giltesa/SmartHome/2. Touch switch/2. Gerbers/1. Touch Switch/Touch Switch - 2017-10 v2.0/Images/SmartHome - Switch Touch.GBO.png

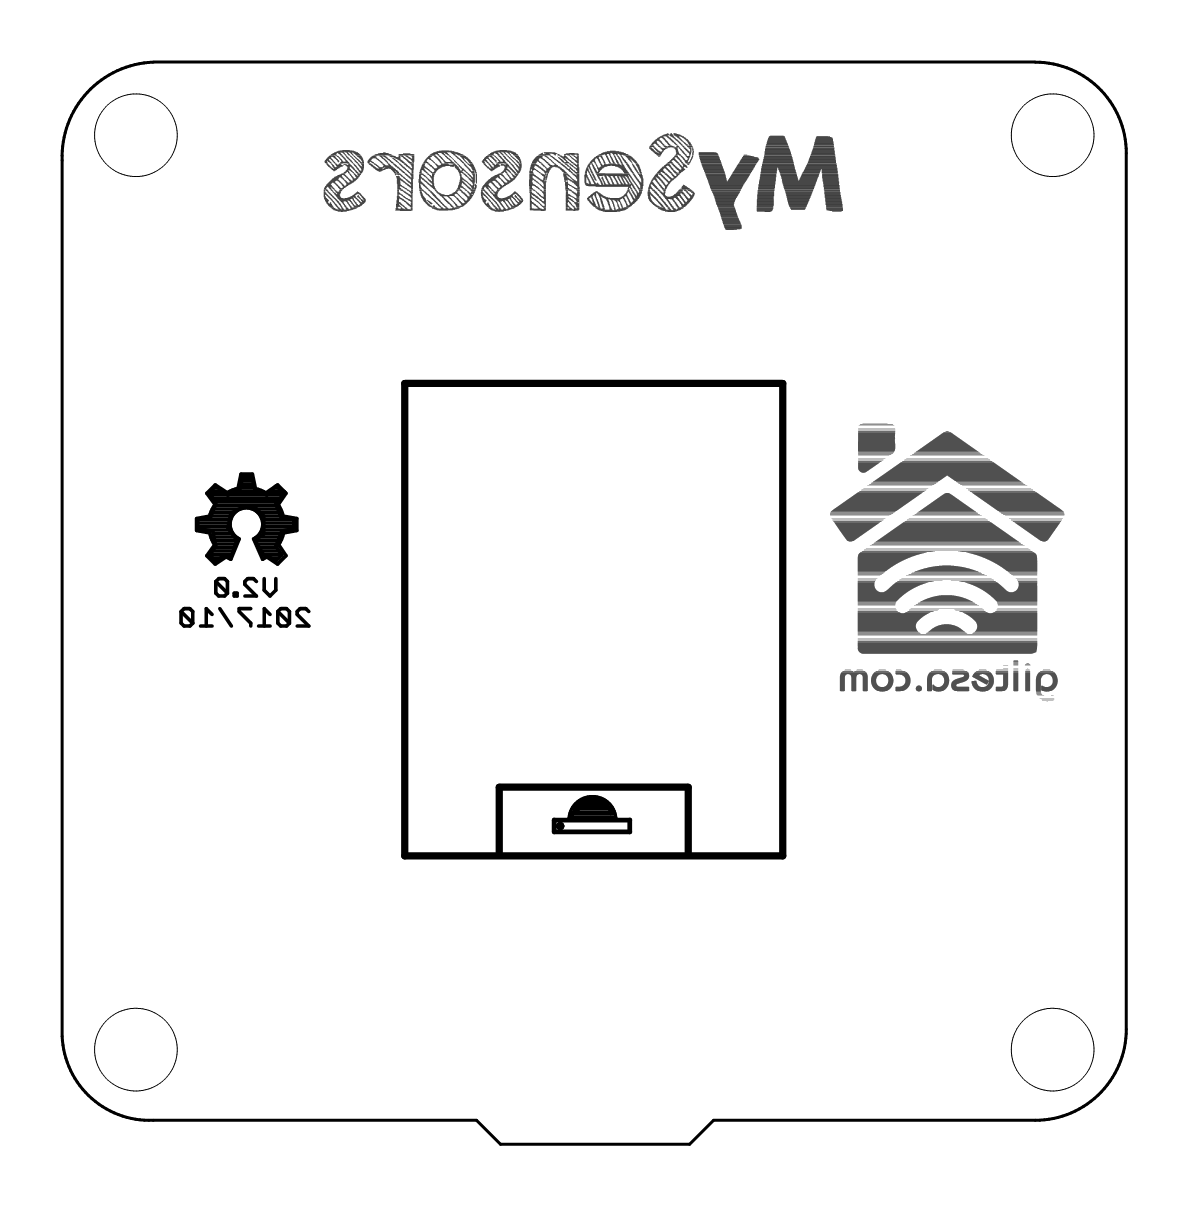
2. Touch switch/2. Gerbers/1. Touch Switch/Touch Switch - 2017-10 v2.0/Images/SmartHome - Switch Touch.GBO.png
