giltesa/SmartHome/2. Touch switch/2. Gerbers/2. Relay Switch/Relay Switch - 2017-10 v1.0/Images/SmartHome - Switch Relay.GBP.png

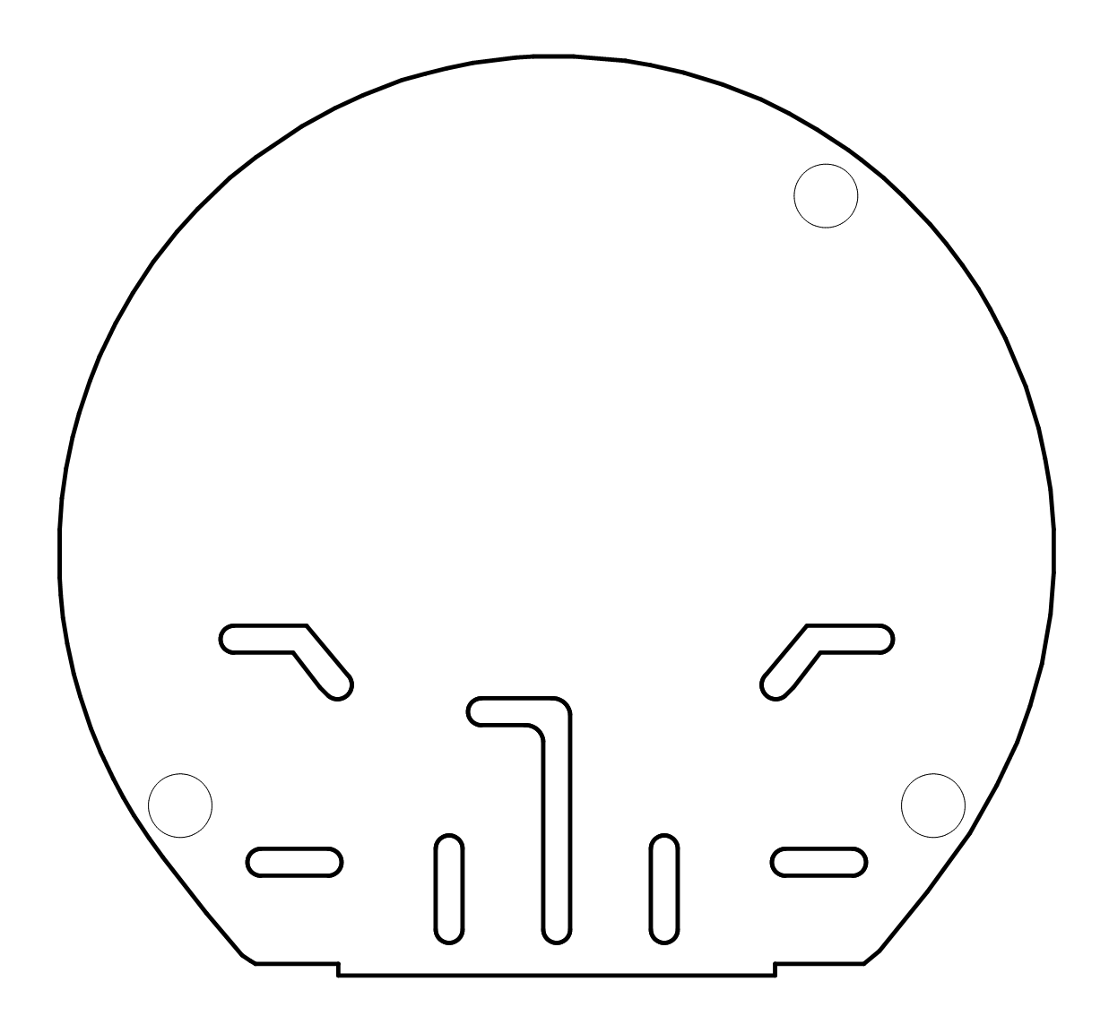
2. Touch switch/2. Gerbers/2. Relay Switch/Relay Switch - 2017-10 v1.0/Images/SmartHome - Switch Relay.GBP.png
