giltesa/SmartHome/2. Touch switch/2. Gerbers/2. Relay Switch/Relay Switch - 2017-12 v1.1/Images/SmartHome - Switch Relay.GTO.png

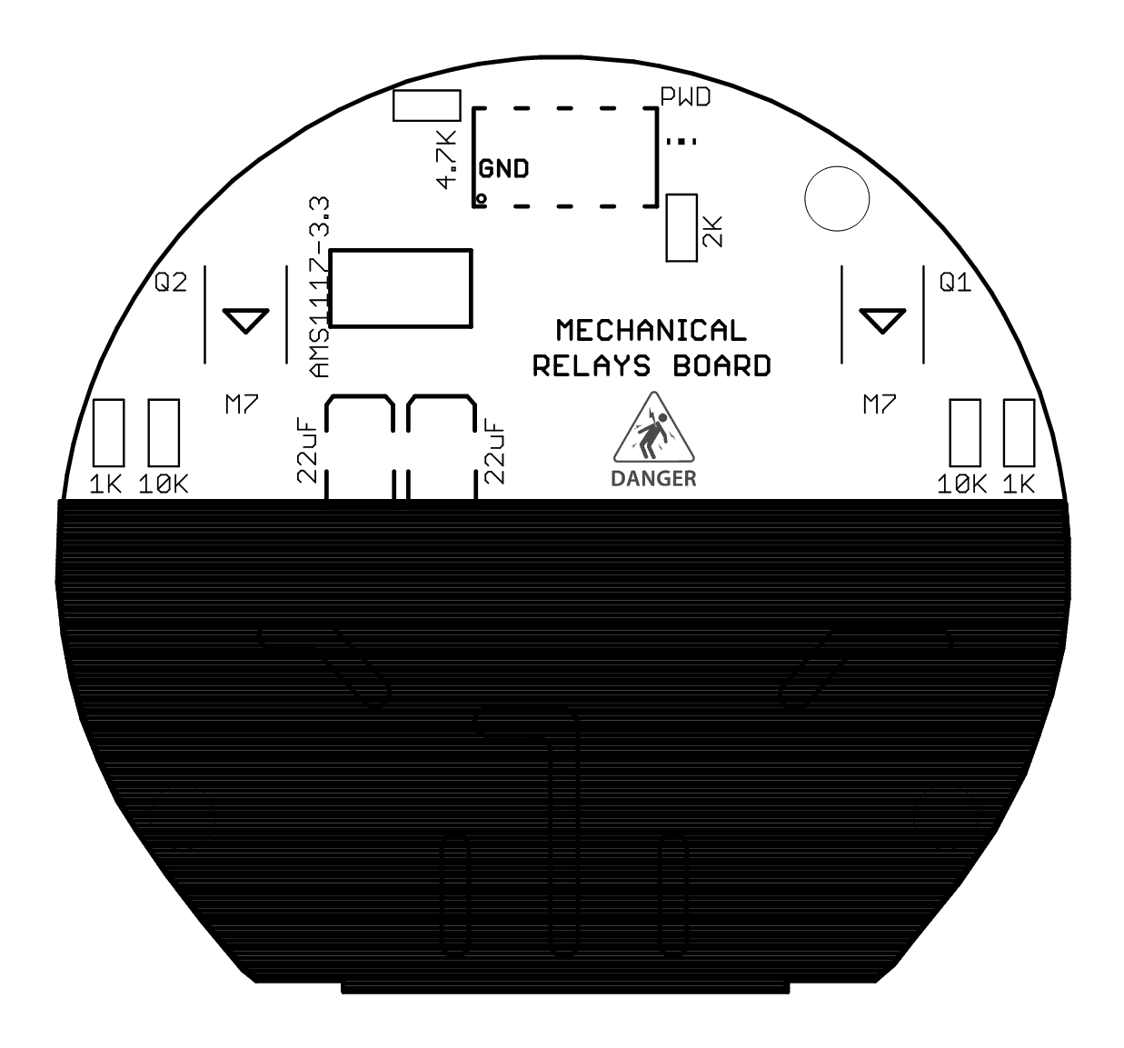
2. Touch switch/2. Gerbers/2. Relay Switch/Relay Switch - 2017-12 v1.1/Images/SmartHome - Switch Relay.GTO.png
