giltesa/SmartHome/2. Touch switch/2. Gerbers/2. Relay Switch/Relay Switch - 2018-03 v1.2/Images/Relay Switch.GBP.png

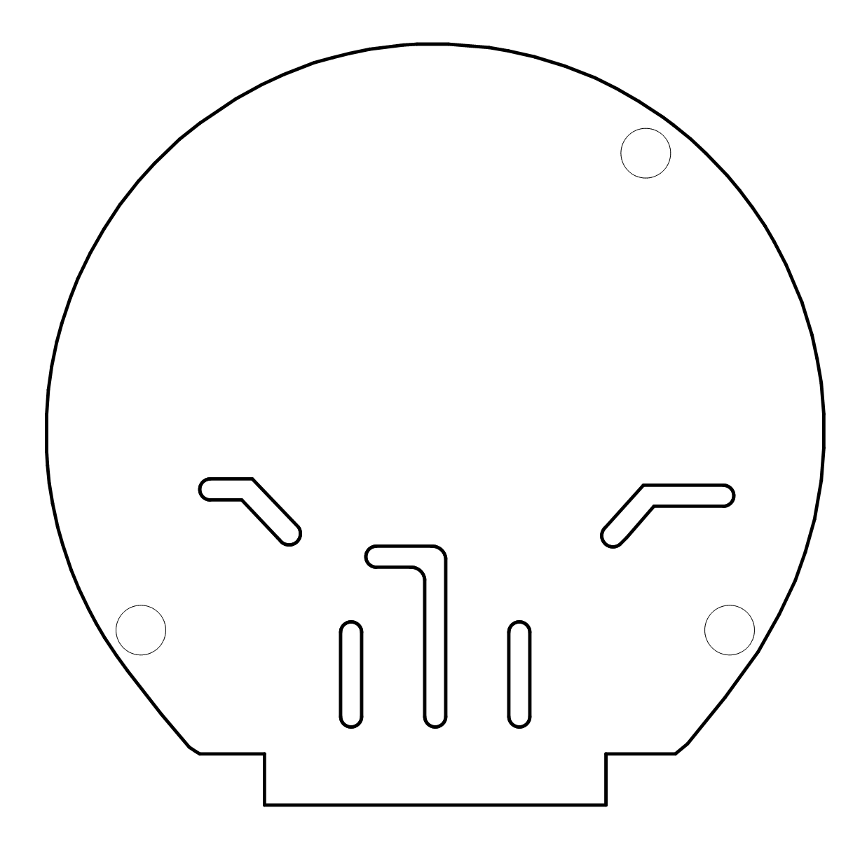
2. Touch switch/2. Gerbers/2. Relay Switch/Relay Switch - 2018-03 v1.2/Images/Relay Switch.GBP.png
