giltesa/SmartHome/2. Touch switch/2. Gerbers/3. Triac Switch/Triac Switch - 2018-03 v1.0/Images/SmartHome - Triac Switch.GTL.png

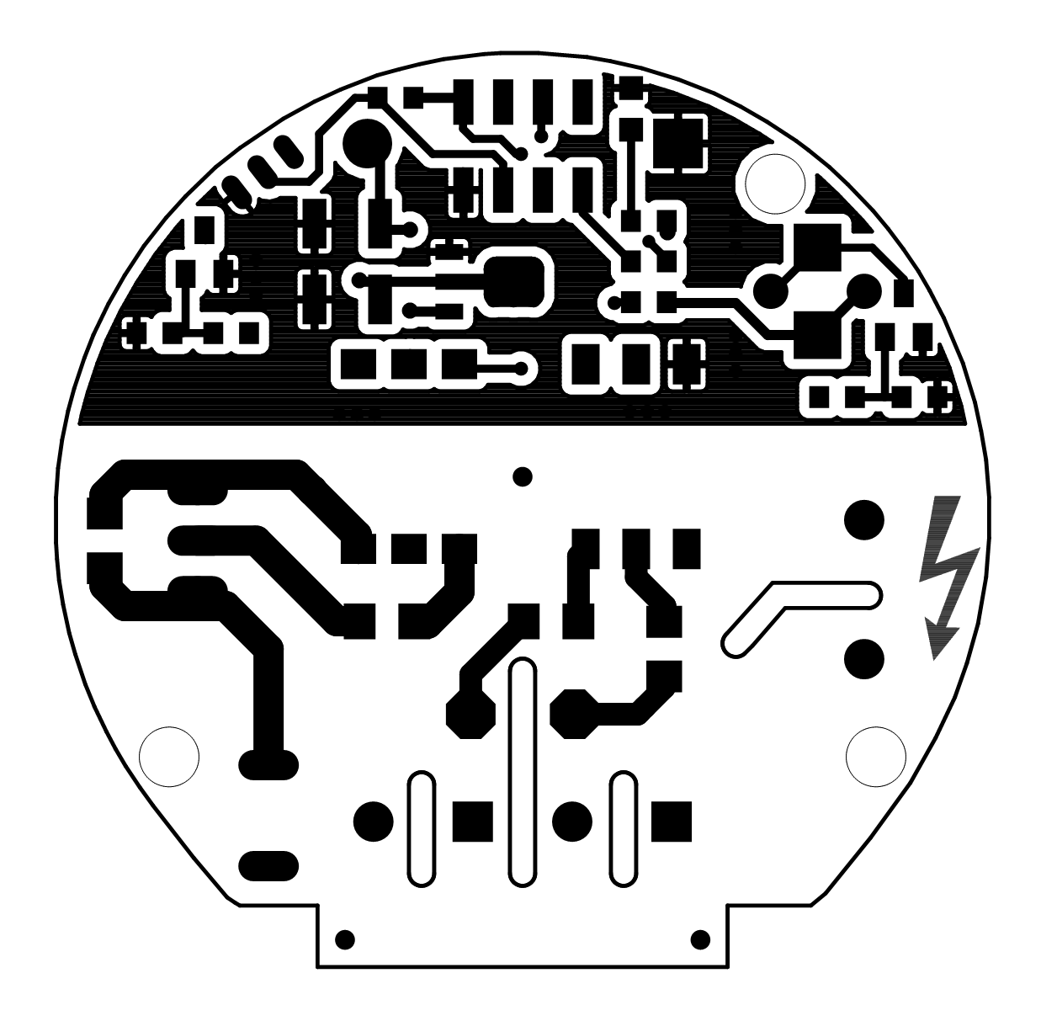
2. Touch switch/2. Gerbers/3. Triac Switch/Triac Switch - 2018-03 v1.0/Images/SmartHome - Triac Switch.GTL.png
