giltesa/SmartHome/2. Touch switch/3. Renders/2. Relay Switch_1.png

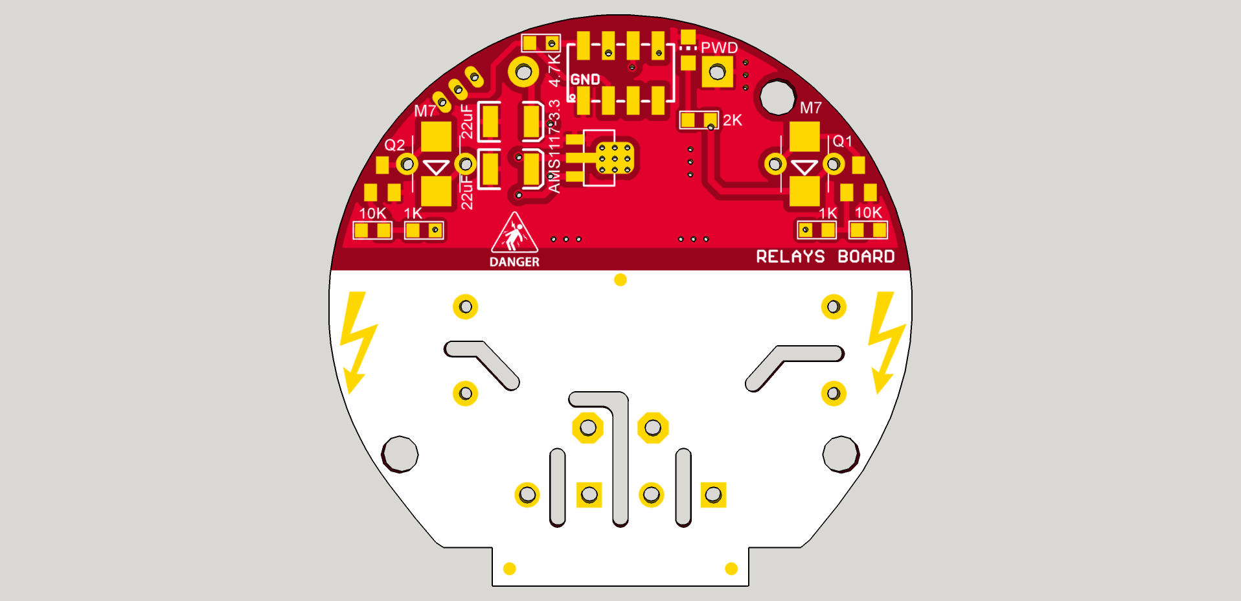
2. Touch switch/3. Renders/2. Relay Switch_1.png
