giltesa/SmartHome/2. Touch switch/3. Renders/2. Relay Switch_2.png

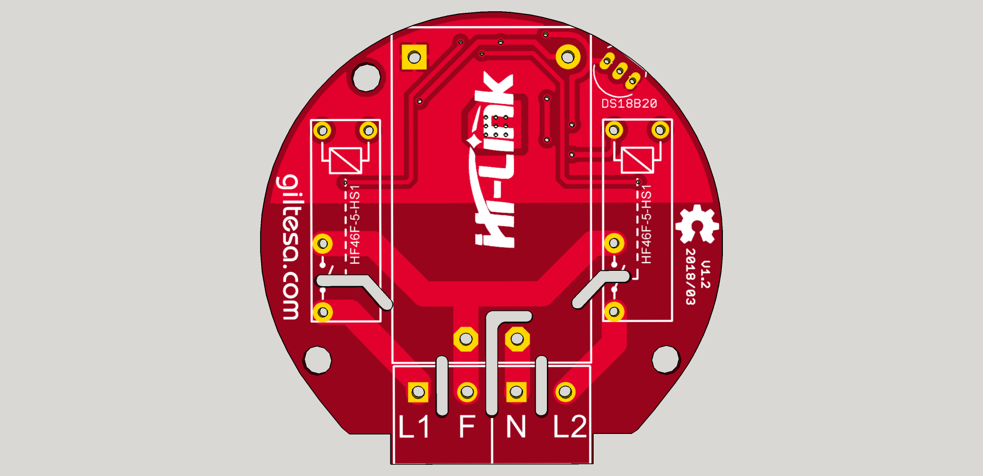
2. Touch switch/3. Renders/2. Relay Switch_2.png
