giltesa/SmartHome/2. Touch switch/3. Renders/Sketchup Enclosure/Switch Relay v3.png

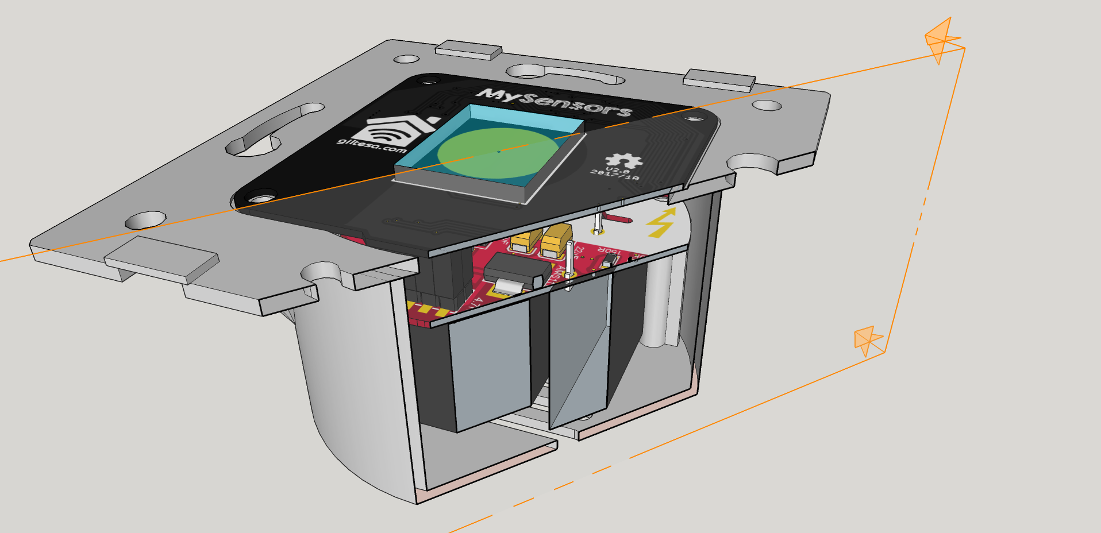
2. Touch switch/3. Renders/Sketchup Enclosure/Switch Relay v3.png
