giltesa/SmartHome/2. Touch switch/3. Renders/Touch Switch.png

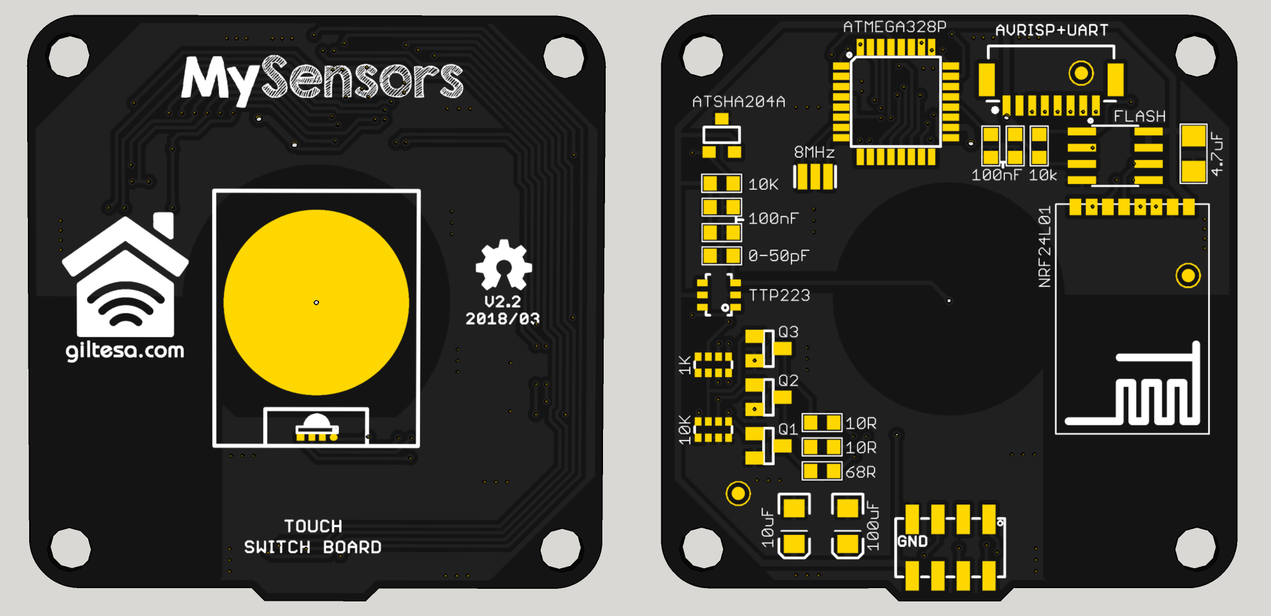
2. Touch switch/3. Renders/Touch Switch.png
