giltesa/SmartHome/2. Touch switch/4. Documentation/1. MCU Board/Fuses ATmega328p 8Mhz 3.3V_1.png

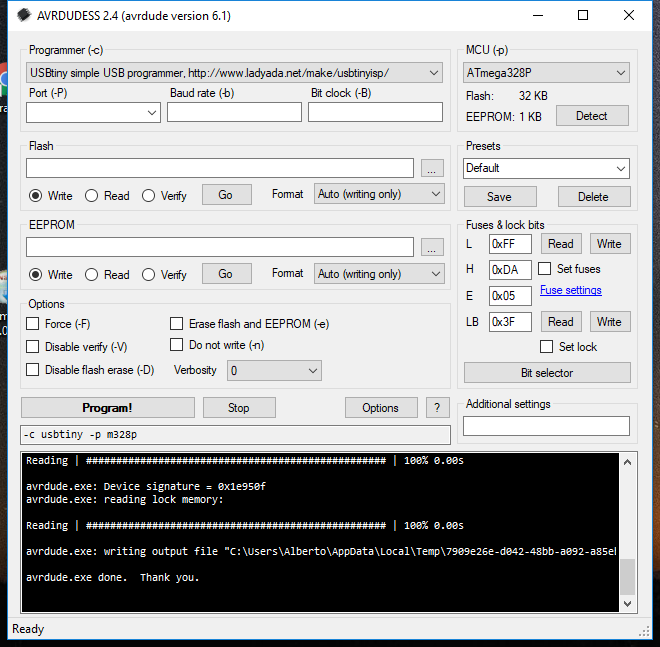
2. Touch switch/4. Documentation/1. MCU Board/Fuses ATmega328p 8Mhz 3.3V_1.png
