giltesa/SmartHome/2. Touch switch/4. Documentation/1. MCU Board/LED RGB.JPG

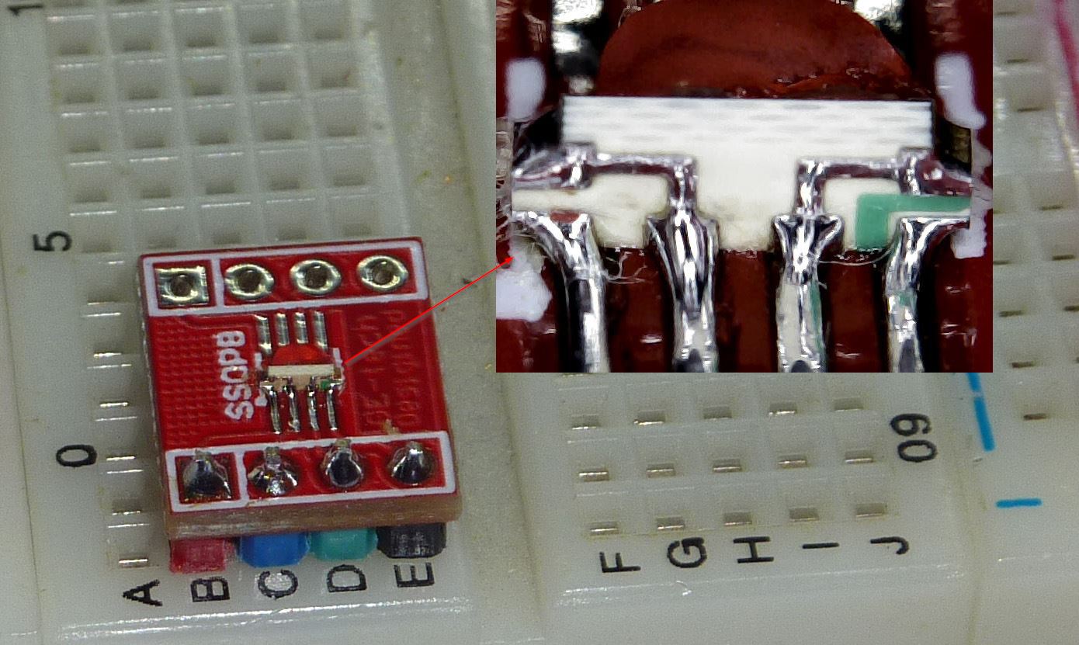
2. Touch switch/4. Documentation/1. MCU Board/LED RGB.JPG
