giltesa/SmartHome/2. Touch switch/4. Documentation/2. Relay Board/Connector AC 5mm.jpg

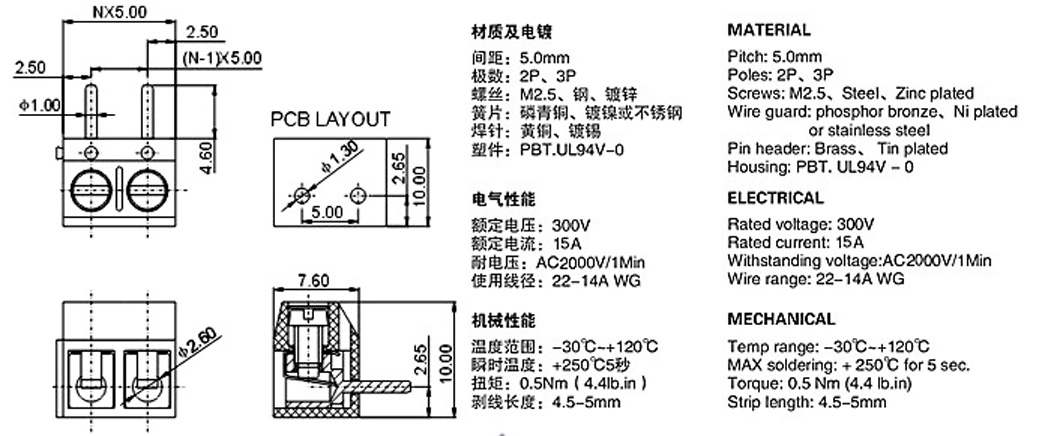
2. Touch switch/4. Documentation/2. Relay Board/Connector AC 5mm.jpg
