giltesa/SmartHome/2. Touch switch/6. Photos/Smarthome_Touch_Switch_Relay_05.JPG

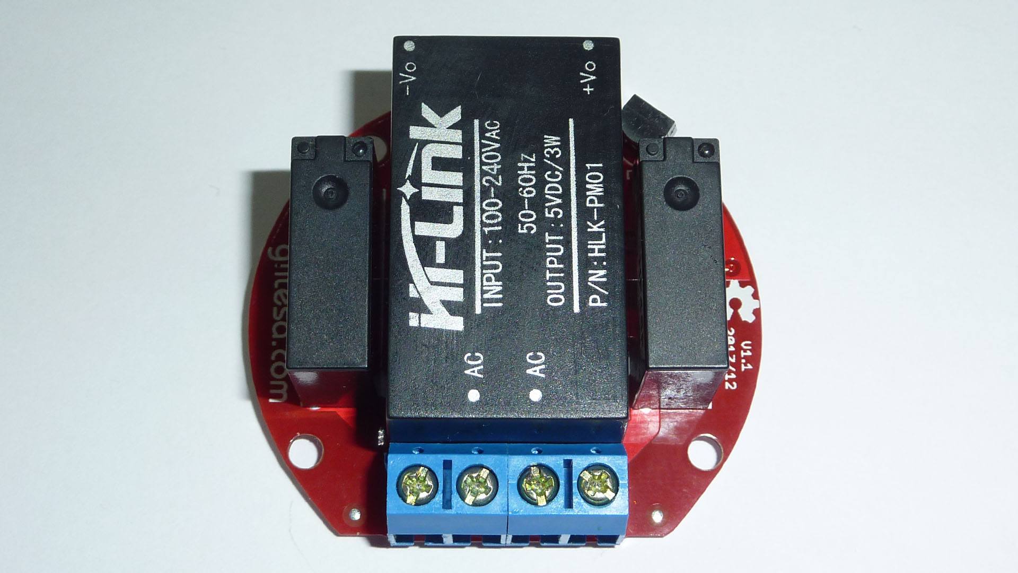
2. Touch switch/6. Photos/Smarthome_Touch_Switch_Relay_05.JPG
