giltesa/SmartHome/3. Sensor/2. Gerbers/Images/Sensor.GBL.png

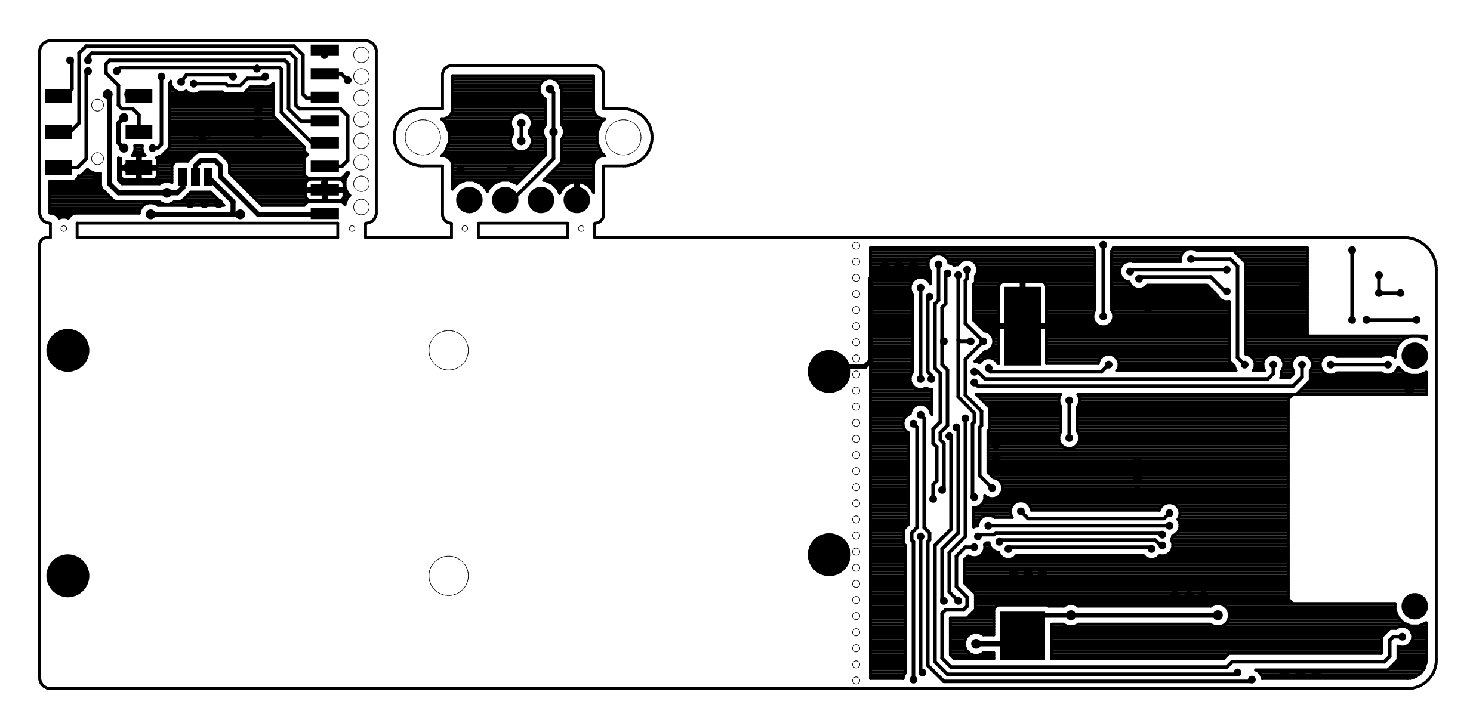
3. Sensor/2. Gerbers/Images/Sensor.GBL.png
