giltesa/SmartHome/3. Sensor/2. Gerbers/Images/Sensor.GBO.png

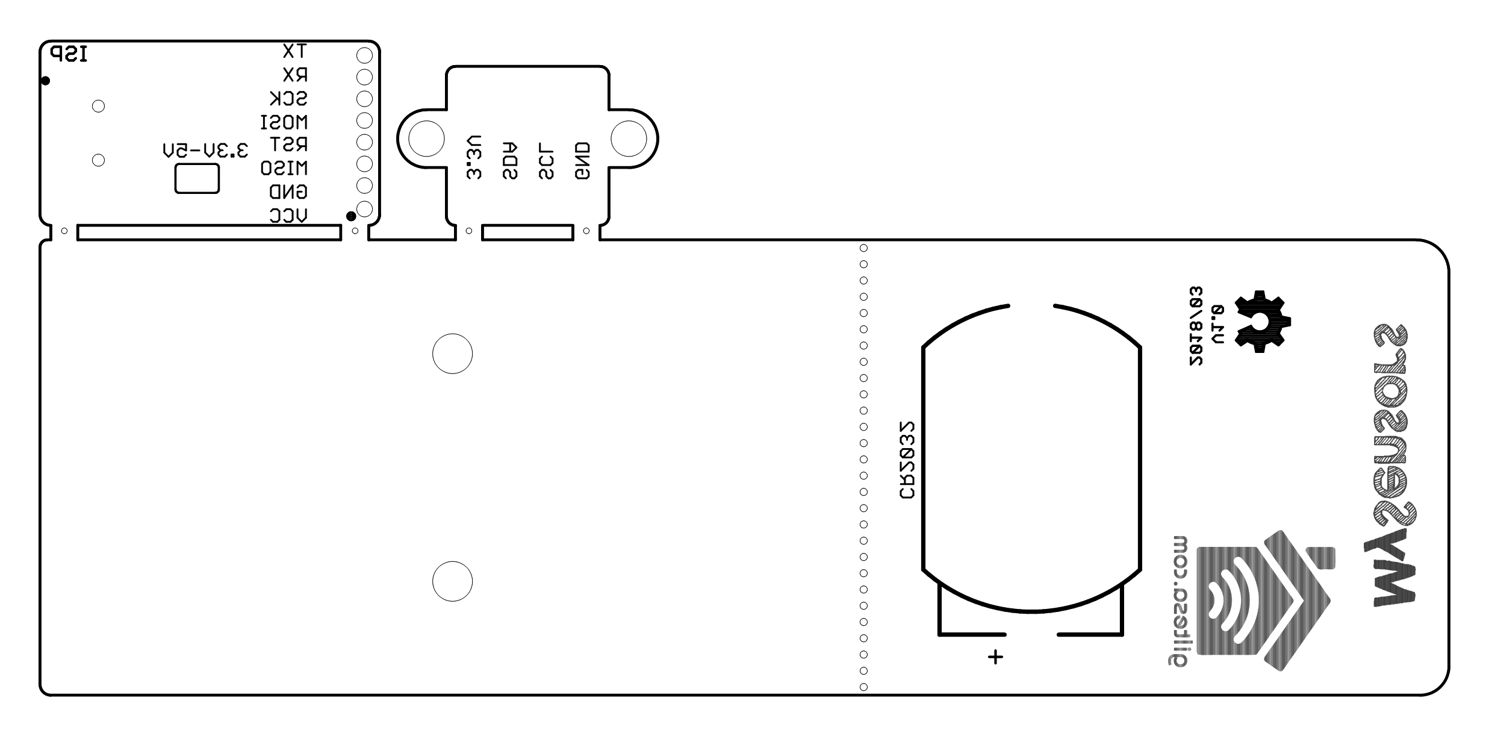
3. Sensor/2. Gerbers/Images/Sensor.GBO.png
