giltesa/SmartHome/3. Sensor/2. Gerbers/Images/Sensor.GBP.png

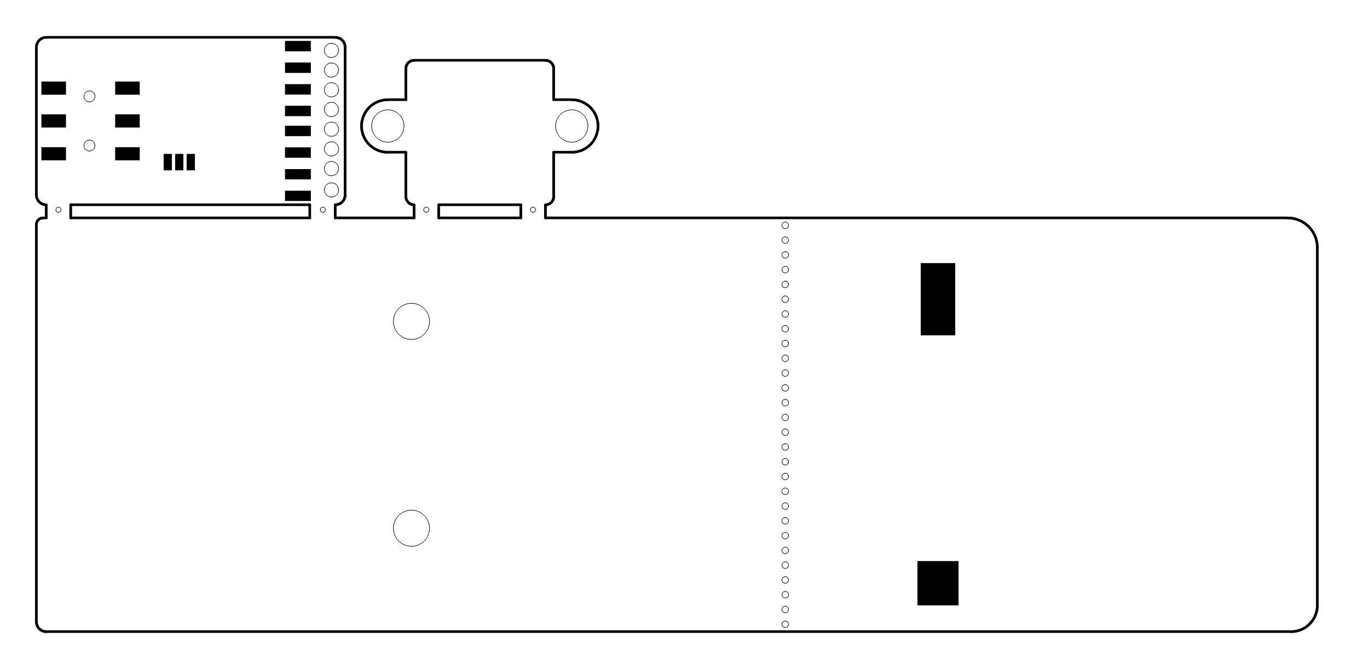
3. Sensor/2. Gerbers/Images/Sensor.GBP.png
