giltesa/SmartHome/3. Sensor/2. Gerbers/Images/Sensor.GBS.png

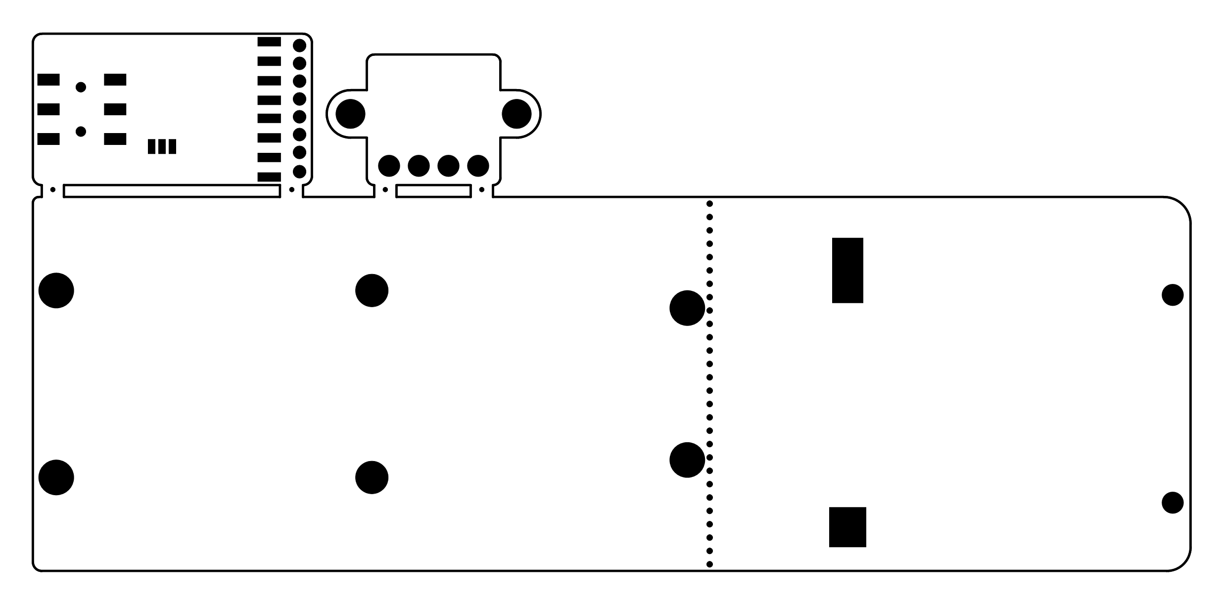
3. Sensor/2. Gerbers/Images/Sensor.GBS.png
