giltesa/SmartHome/3. Sensor/2. Gerbers/Images/Sensor.GML.png

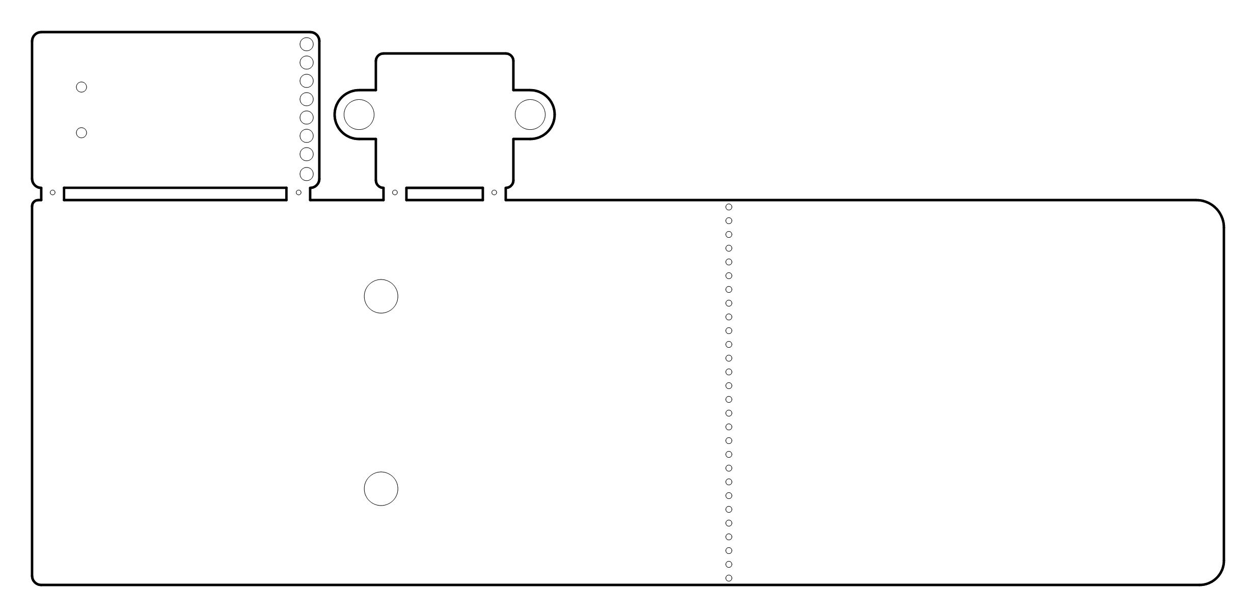
3. Sensor/2. Gerbers/Images/Sensor.GML.png
