giltesa/SmartHome/3. Sensor/2. Gerbers/Images/Sensor.GTL.png

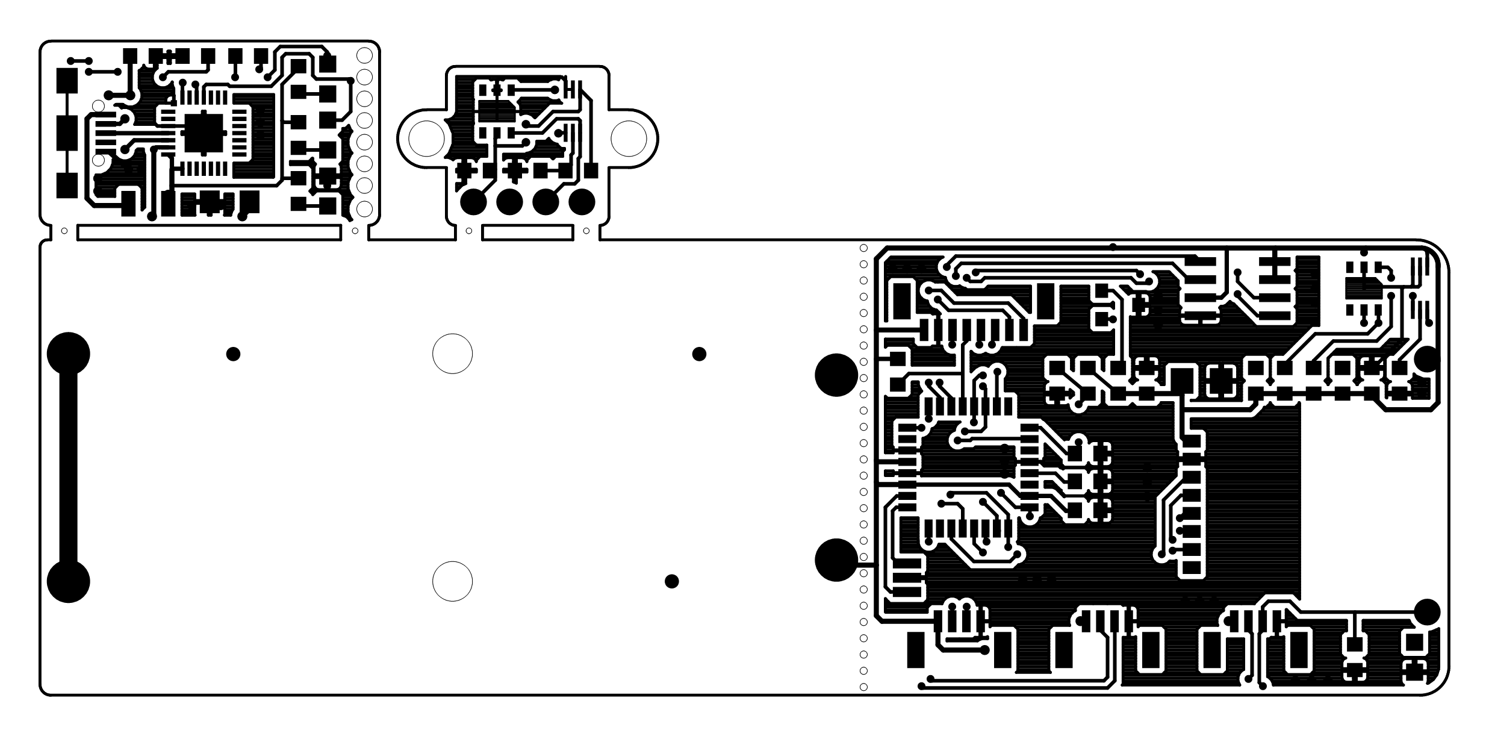
3. Sensor/2. Gerbers/Images/Sensor.GTL.png
