giltesa/SmartHome/3. Sensor/2. Gerbers/Images/Sensor.GTP.png

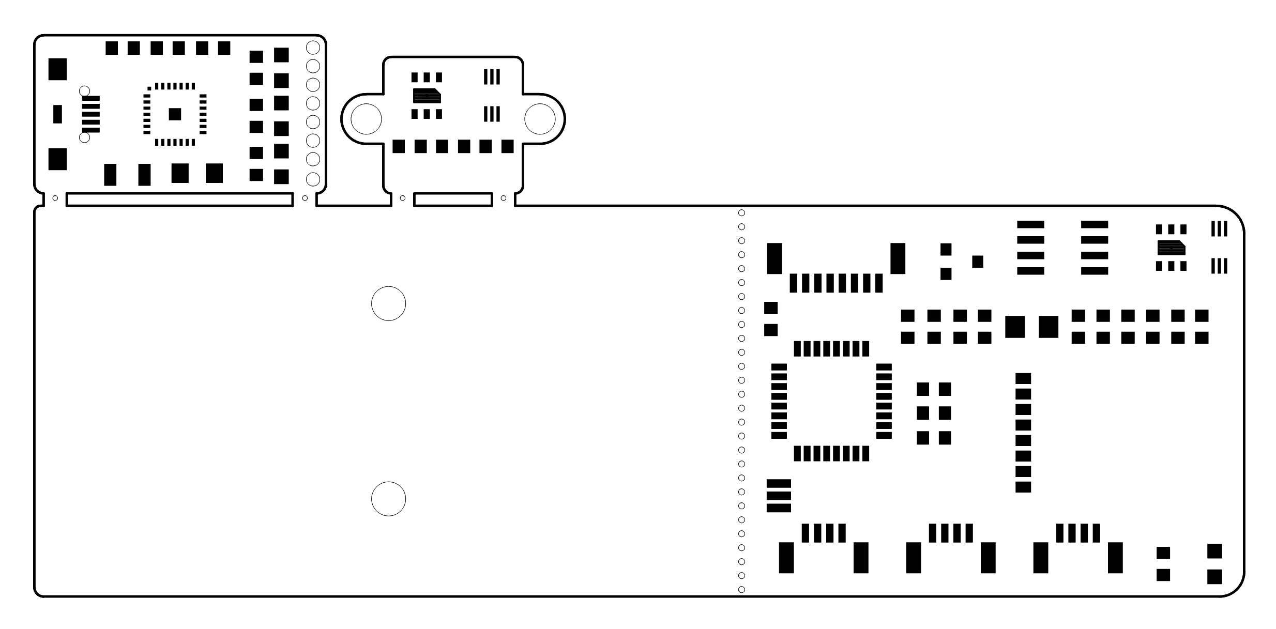
3. Sensor/2. Gerbers/Images/Sensor.GTP.png
