giltesa/SmartHome/3. Sensor/2. Gerbers/Images/Sensor.GTS.png

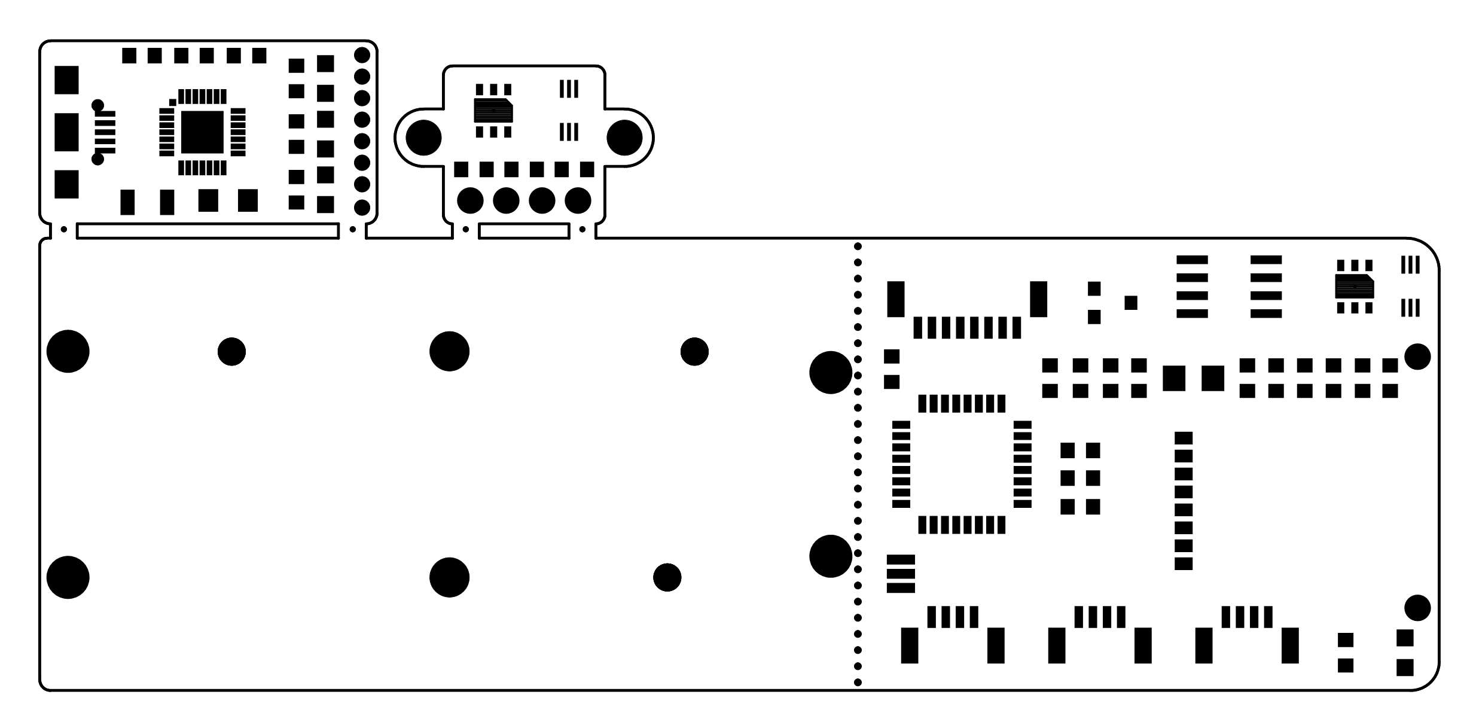
3. Sensor/2. Gerbers/Images/Sensor.GTS.png
