giltesa/SmartHome/3. Sensor/3. Renders/Sensor_1.png

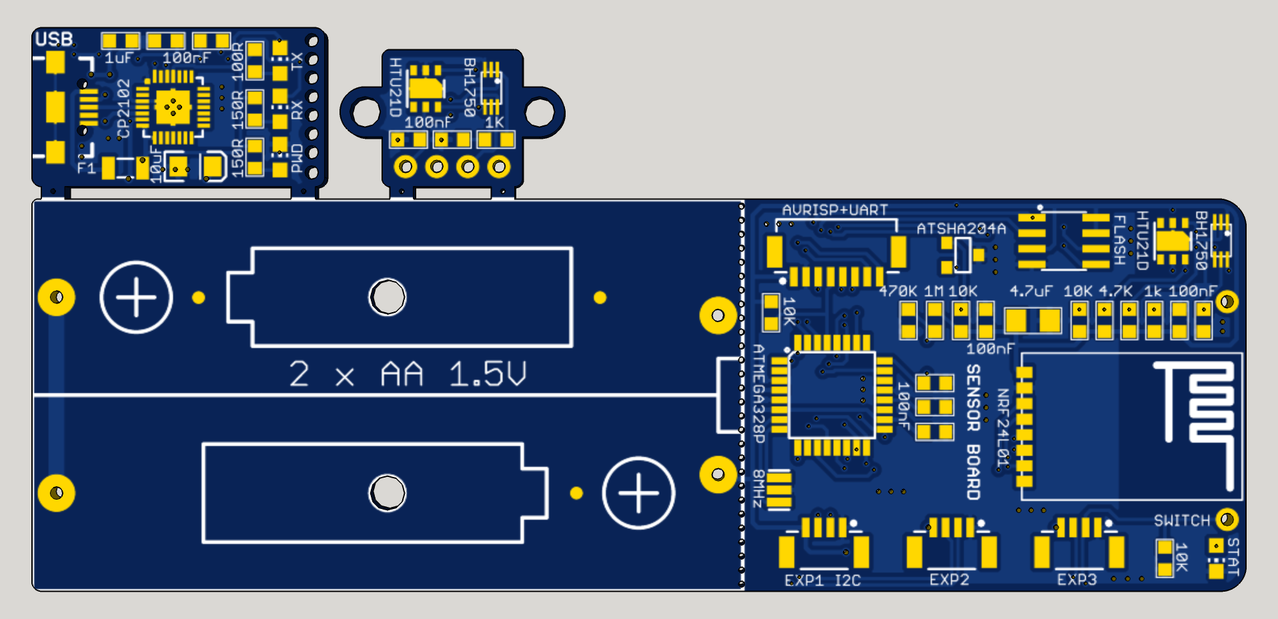
3. Sensor/3. Renders/Sensor_1.png
