giltesa/SmartHome/3. Sensor/3. Renders/Sensor_2.png

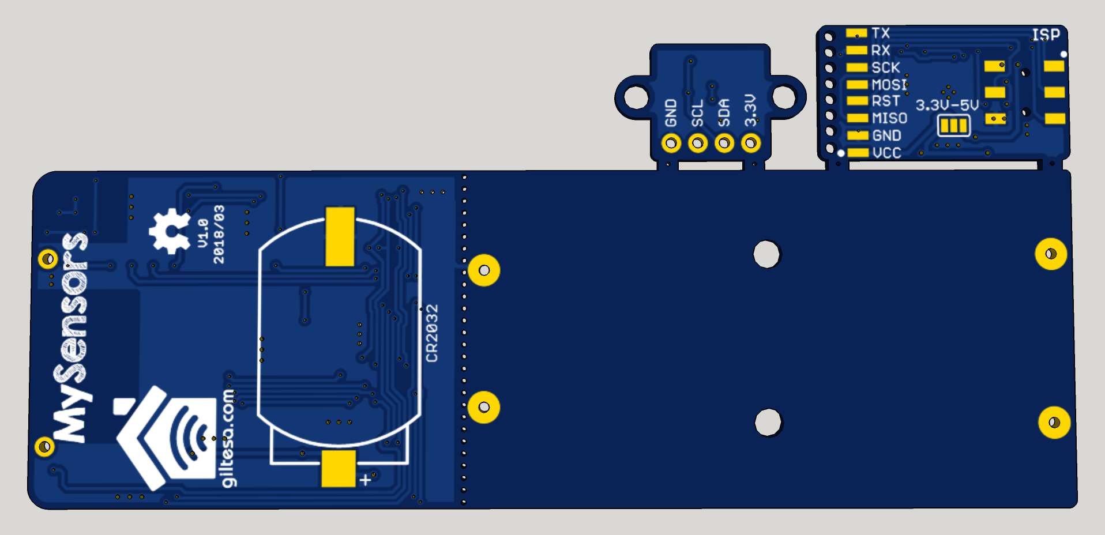
3. Sensor/3. Renders/Sensor_2.png
