giltesa/SmartHome/3. Sensor/6. Photos/External programmer 1.jpg

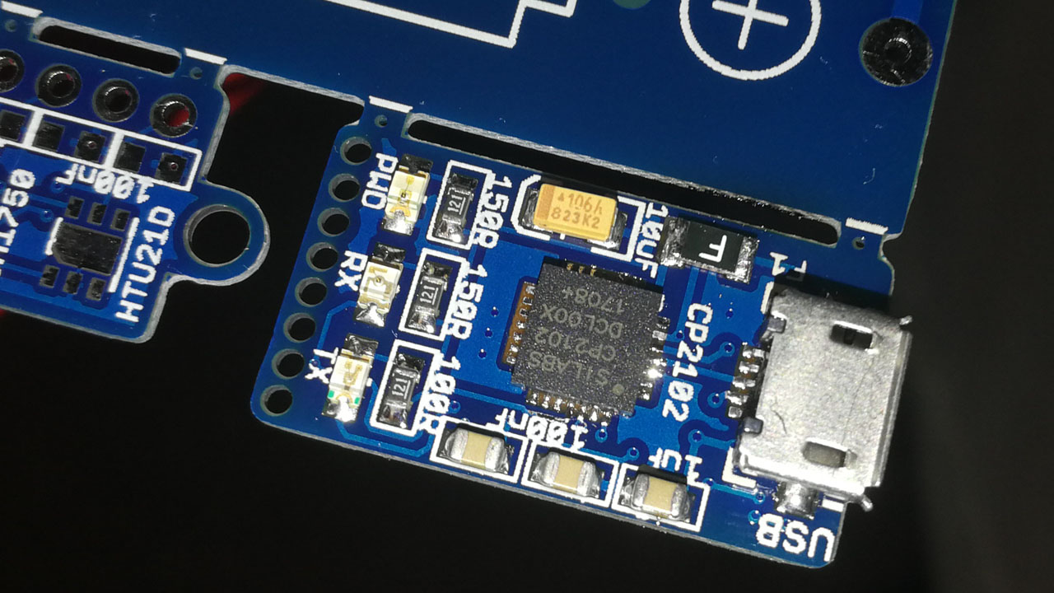
3. Sensor/6. Photos/External programmer 1.jpg
