giltesa/SmartHome/3. Sensor/6. Photos/External programmer 2 ISP.jpg

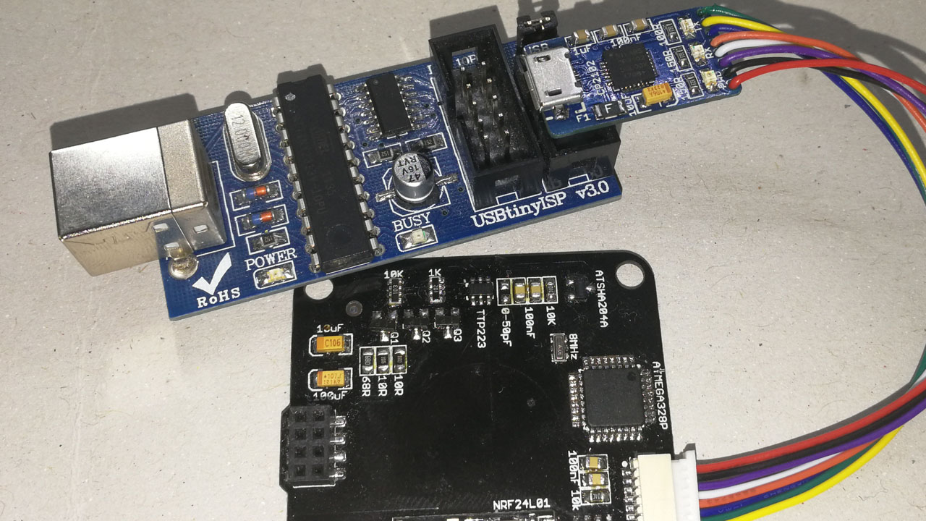
3. Sensor/6. Photos/External programmer 2 ISP.jpg
