giltesa/SmartHome/3. Sensor/6. Photos/External programmer 3 UART.jpg

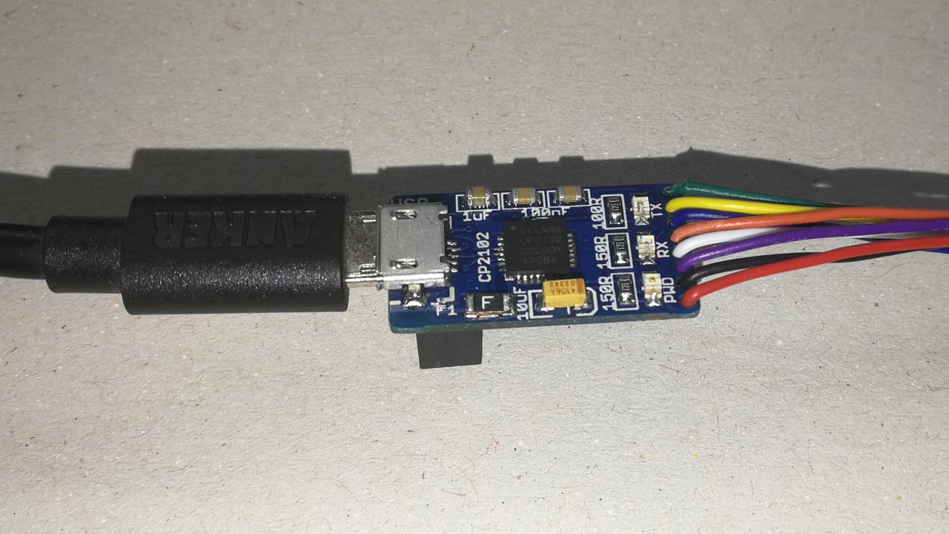
3. Sensor/6. Photos/External programmer 3 UART.jpg
