giltesa/SmartHome/3. Sensor/6. Photos/Sensor 1.jpg

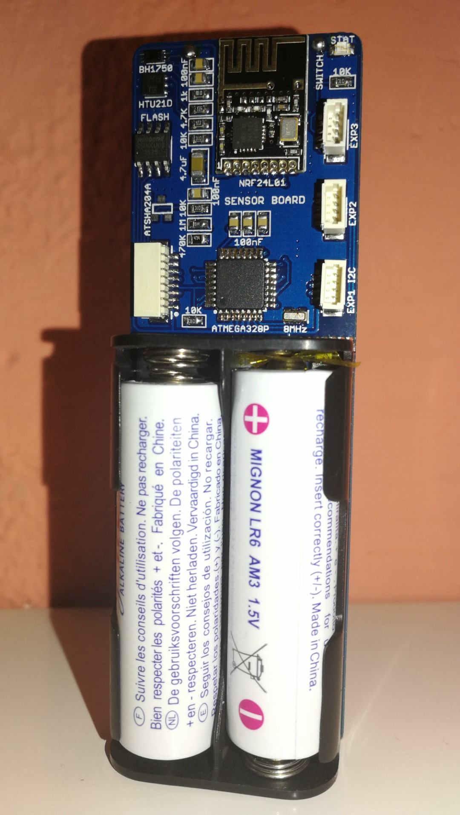
3. Sensor/6. Photos/Sensor 1.jpg
