giltesa/SmartHome/3. Sensor/6. Photos/Sensor 2.jpg

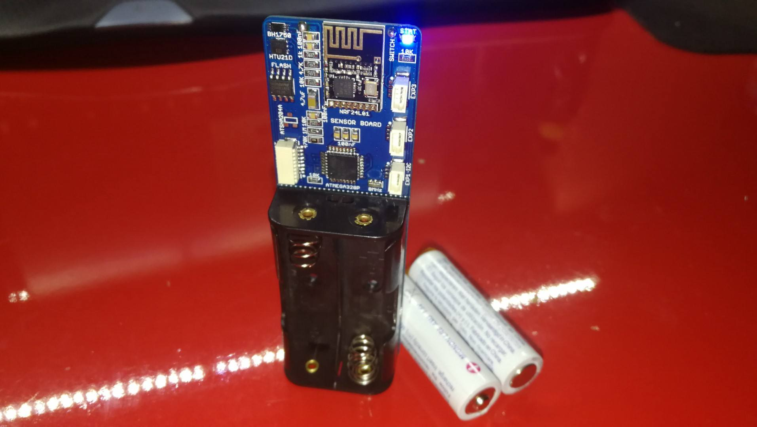
3. Sensor/6. Photos/Sensor 2.jpg
