giltesa/SmartHome/3. Sensor/6. Photos/Sensor 3.jpg

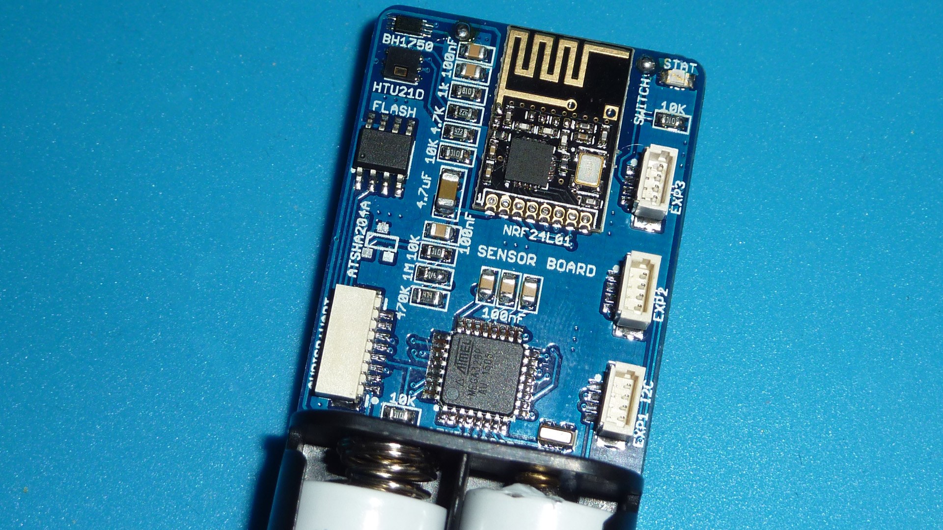
3. Sensor/6. Photos/Sensor 3.jpg
