giltesa/SmartHome/4. Remote Control/2. Gerbers/Images/Remote Control - x2.GBP.png

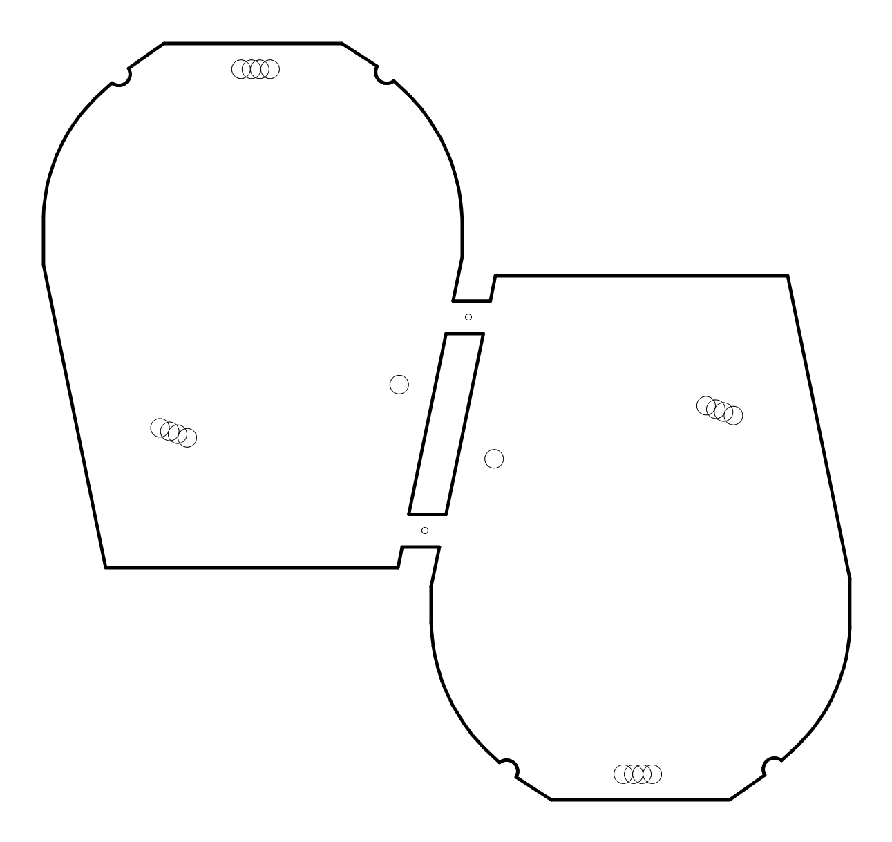
4. Remote Control/2. Gerbers/Images/Remote Control - x2.GBP.png
