giltesa/SmartHome/4. Remote Control/2. Gerbers/Images/Remote Control - x2.GTO.png

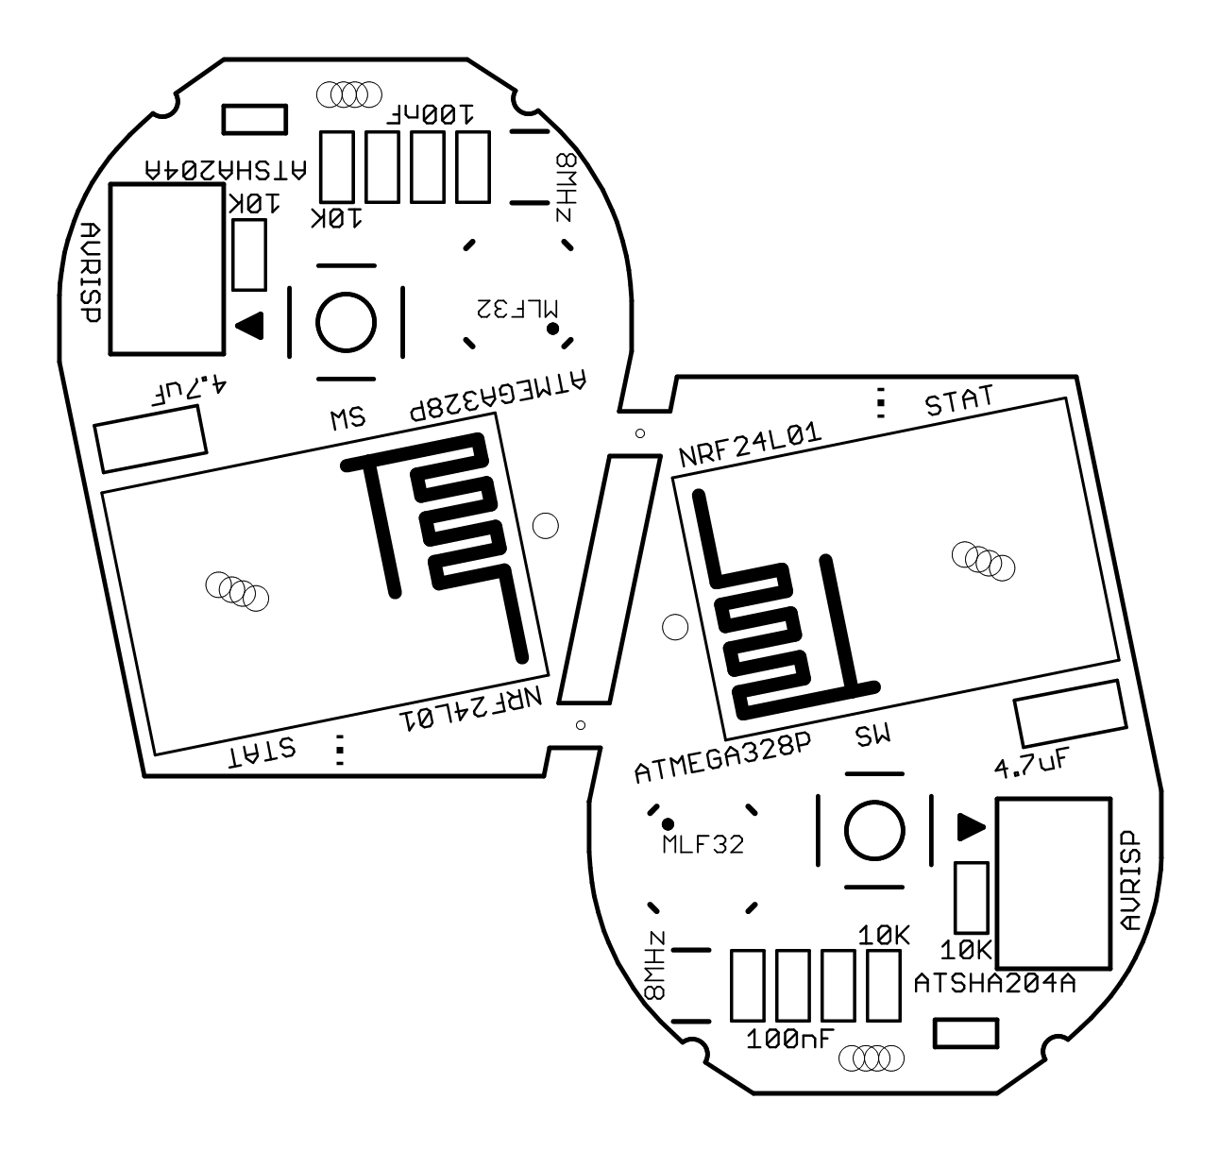
4. Remote Control/2. Gerbers/Images/Remote Control - x2.GTO.png
