giltesa/SmartHome/4. Remote Control/2. Gerbers/Images/Remote Control - x2.GTP.png

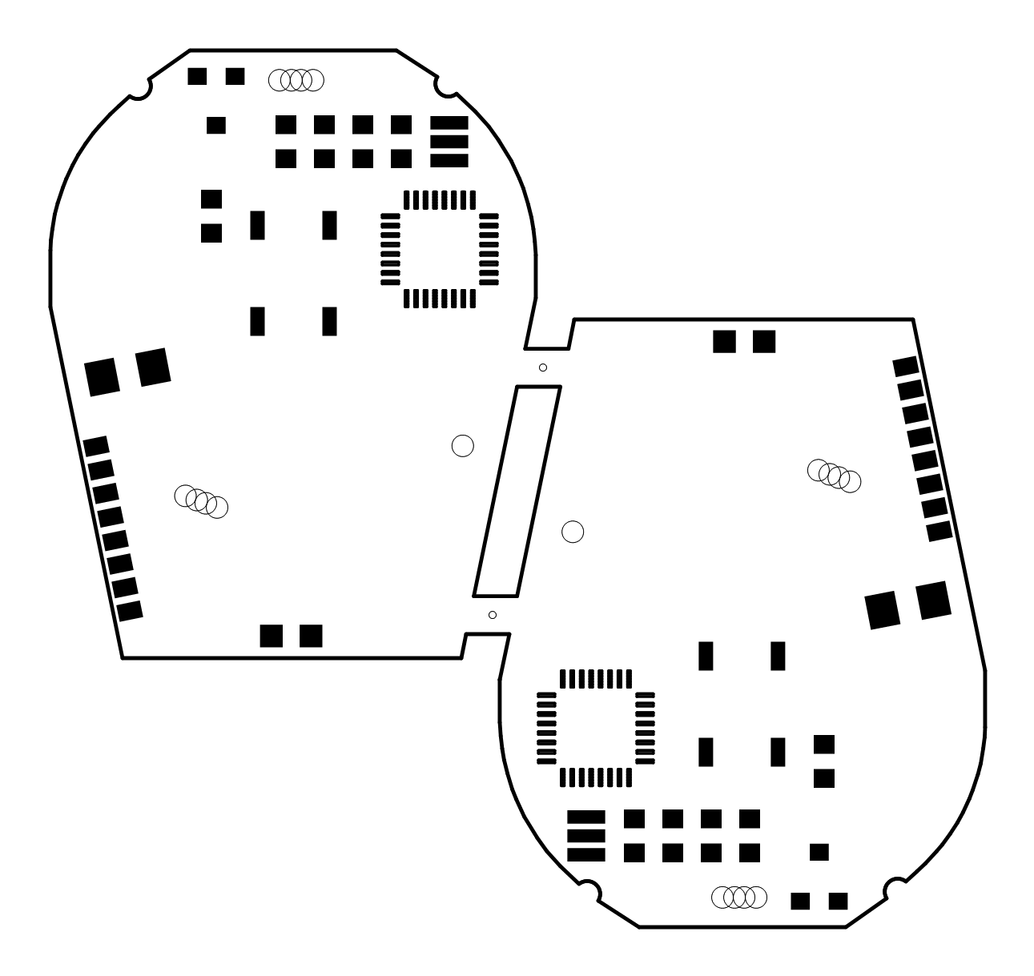
4. Remote Control/2. Gerbers/Images/Remote Control - x2.GTP.png
