giltesa/SmartHome/4. Remote Control/2. Gerbers/Images/Remote Control - x2.GTS.png

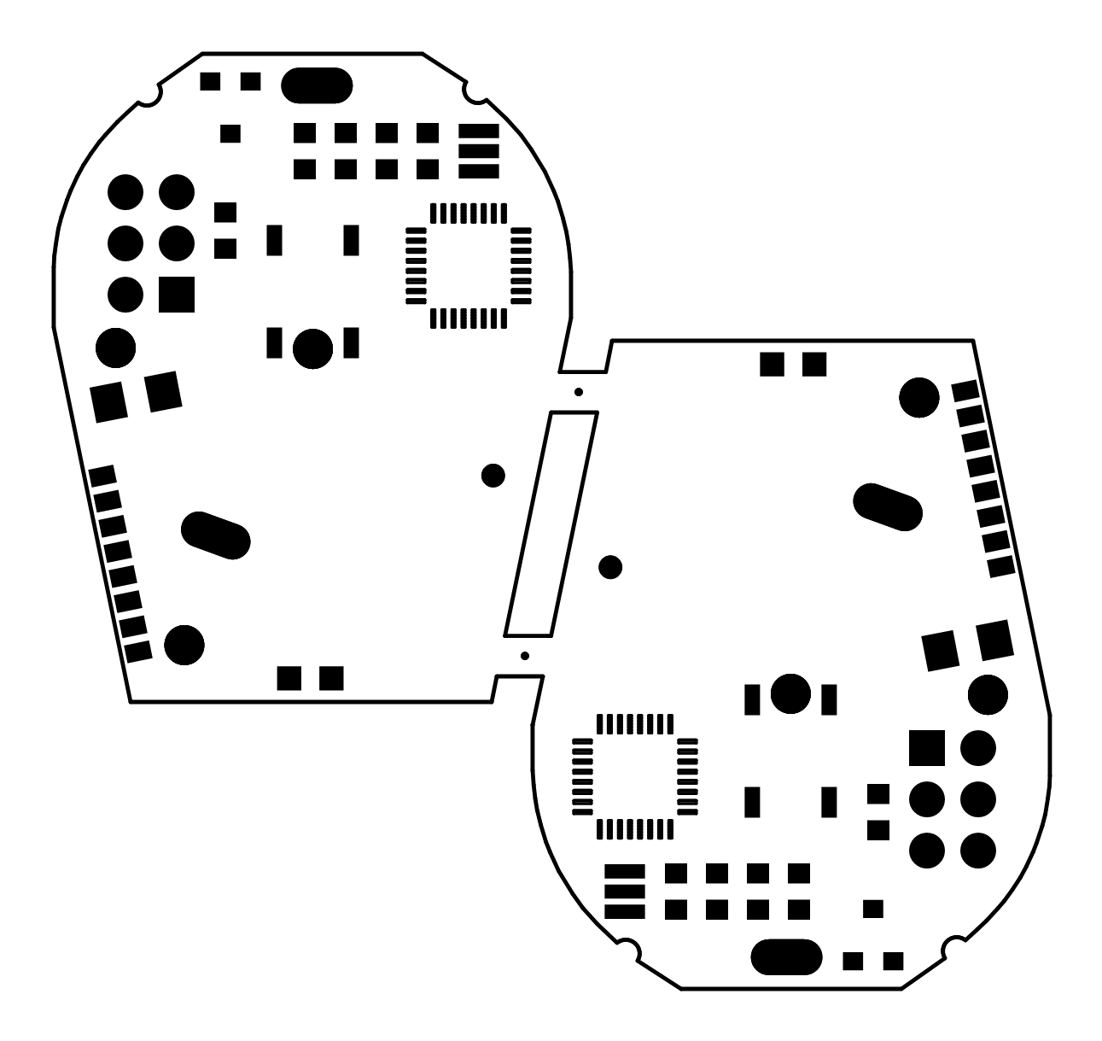
4. Remote Control/2. Gerbers/Images/Remote Control - x2.GTS.png
