giltesa/SmartHome/4. Remote Control/3. Renders/Remote Control RF 1.png

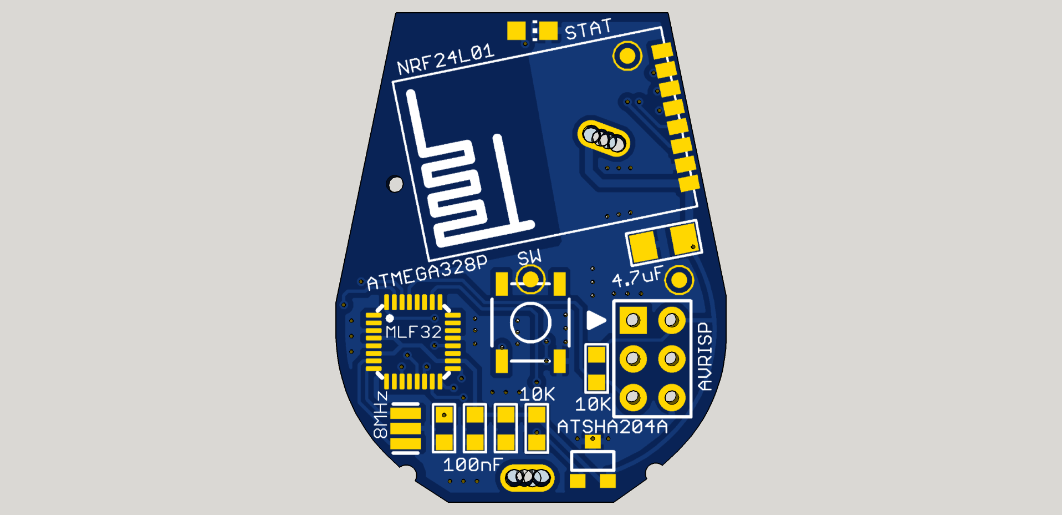
4. Remote Control/3. Renders/Remote Control RF 1.png
