giltesa/SmartHome/4. Remote Control/3. Renders/Remote Control RF 2.png

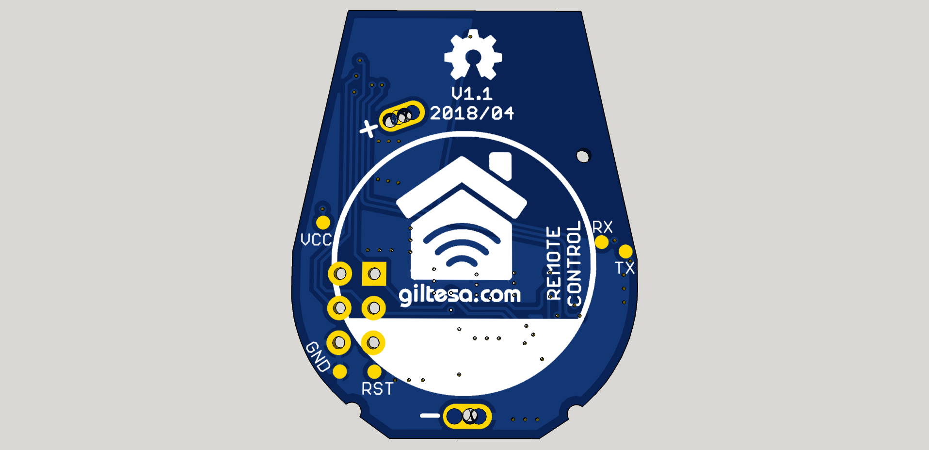
4. Remote Control/3. Renders/Remote Control RF 2.png
