giltesa/SmartHome/4. Remote Control/3. Renders/Remote Control RF 3.png

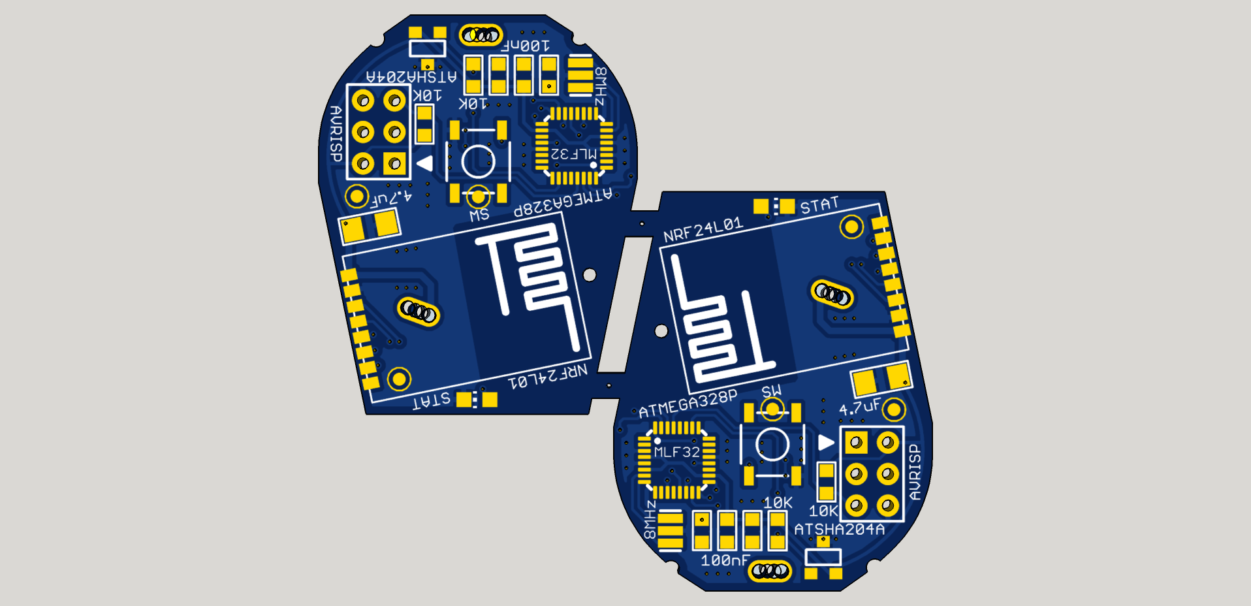
4. Remote Control/3. Renders/Remote Control RF 3.png
