giltesa/SmartHome/4. Remote Control/6. Photos/Catch3602.jpg

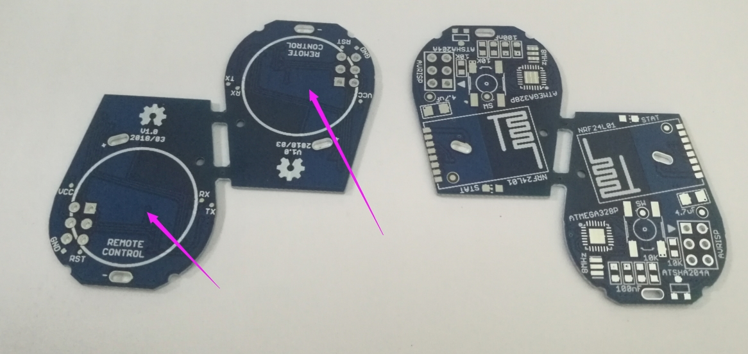
4. Remote Control/6. Photos/Catch3602.jpg
