giltesa/SmartHome/5. LED RGBW Controller/2. Gerbers/Images/LED RGBW Controller.GBL.png

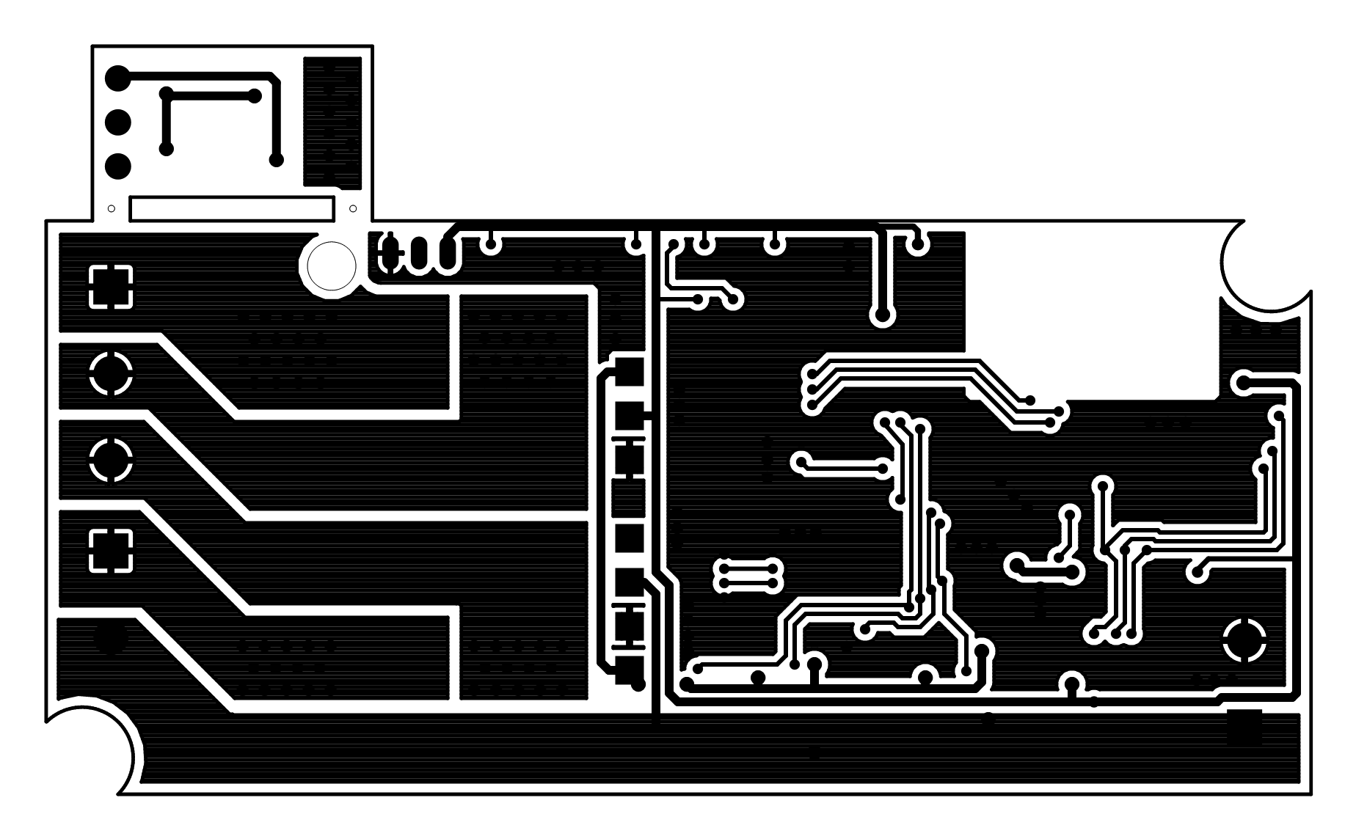
5. LED RGBW Controller/2. Gerbers/Images/LED RGBW Controller.GBL.png
