giltesa/SmartHome/5. LED RGBW Controller/2. Gerbers/Images/LED RGBW Controller.GBP.png

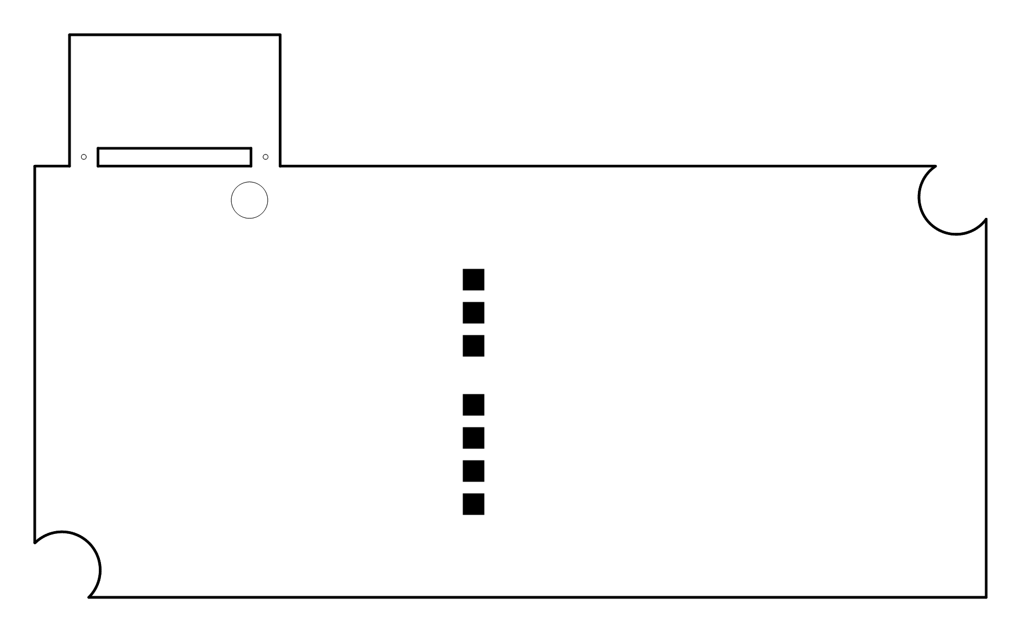
5. LED RGBW Controller/2. Gerbers/Images/LED RGBW Controller.GBP.png
