giltesa/SmartHome/5. LED RGBW Controller/3. Renders/RGBW Controller_2b.png

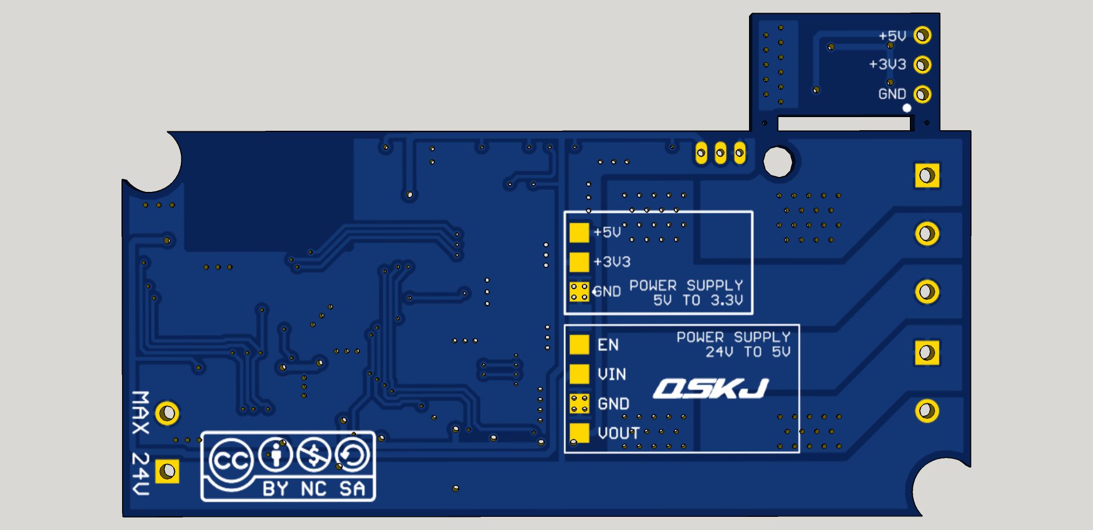
5. LED RGBW Controller/3. Renders/RGBW Controller_2b.png
