giltesa/SmartHome/5. LED RGBW Controller/3. Renders/Sketchup/washer.jpg

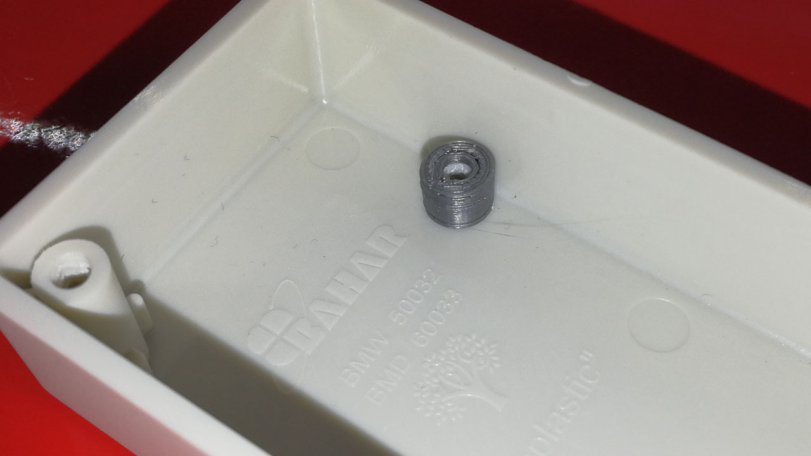
5. LED RGBW Controller/3. Renders/Sketchup/washer.jpg
