giltesa/SmartHome/5. LED RGBW Controller/6. Photos/LED RGBW Controller 4.JPG

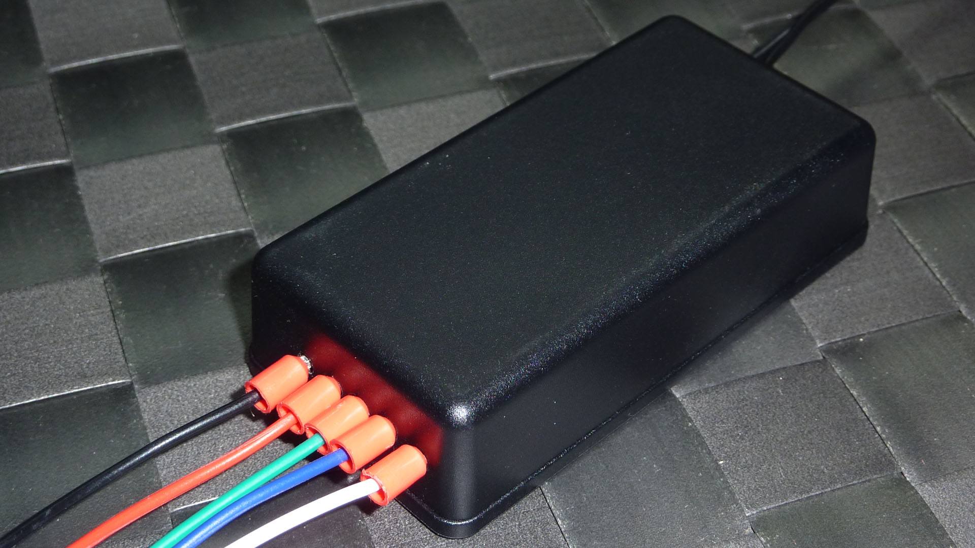
5. LED RGBW Controller/6. Photos/LED RGBW Controller 4.JPG
