giltesa/SmartHome/5. LED RGBW Controller/6. Photos/LED RGBW Controller 6.png

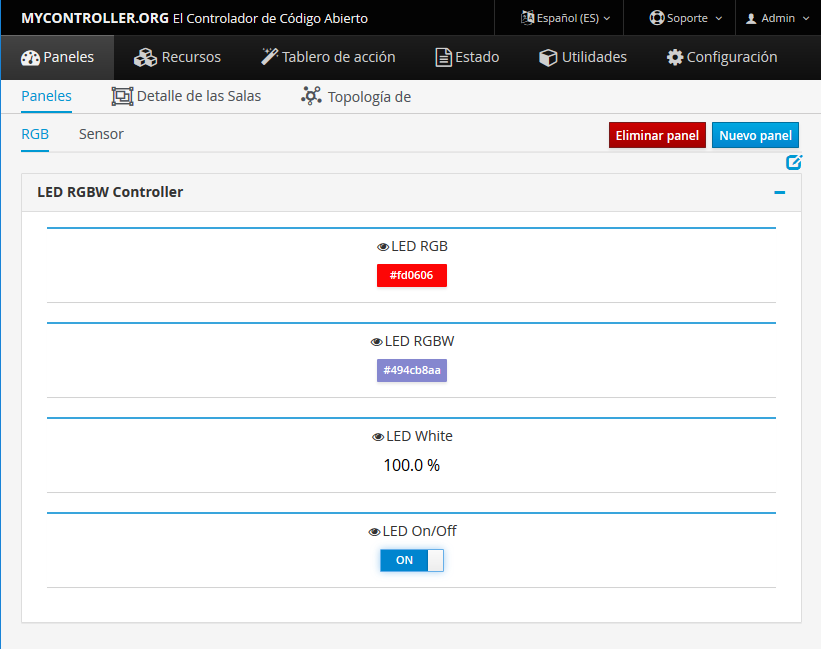
5. LED RGBW Controller/6. Photos/LED RGBW Controller 6.png
