giltesa/SmartHome/7. Current sensor/3. Renders/DinBox 1.png

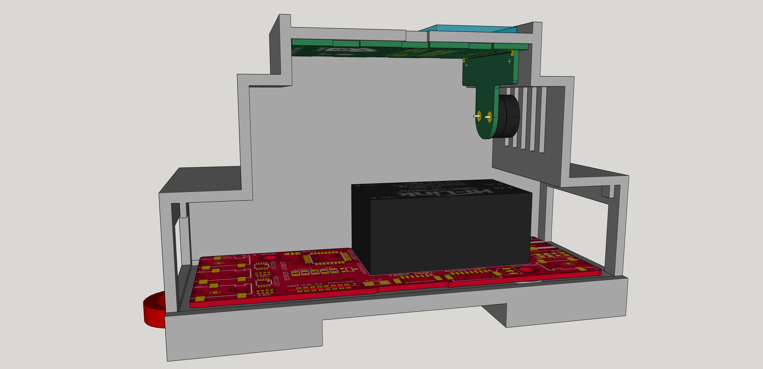
7. Current sensor/3. Renders/DinBox 1.png
