giltesa/SmartHome/7. Current sensor/4. Documentation/touch sticker.png

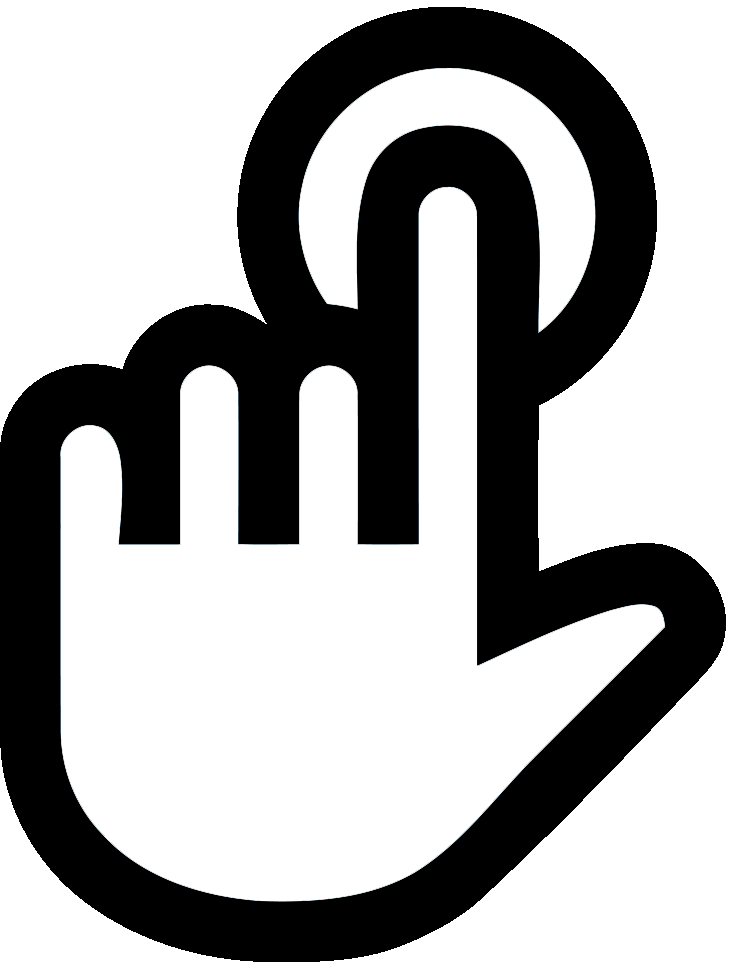
7. Current sensor/4. Documentation/touch sticker.png
