giltesa/SmartHome/5. LED RGBW Controller/3. Renders/Sketchup/Drilling guide.jpg

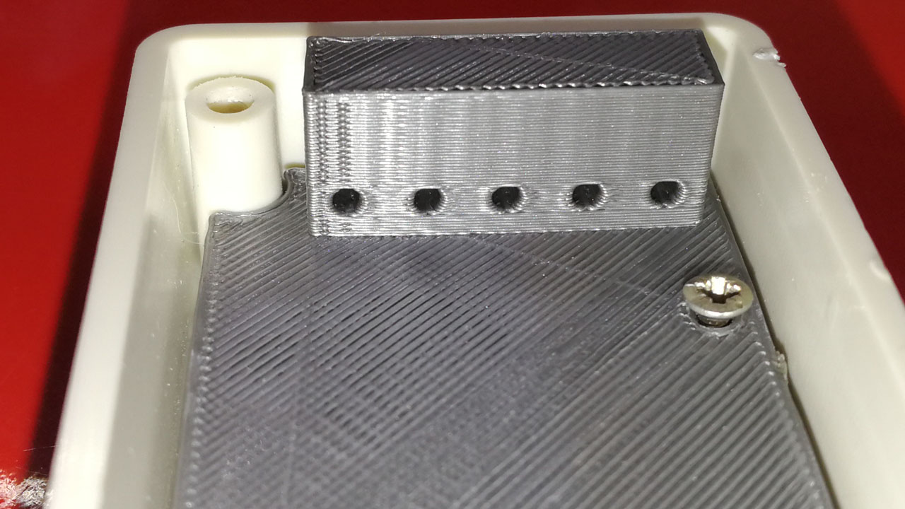
5. LED RGBW Controller/3. Renders/Sketchup/Drilling guide.jpg
