giltesa/SmartHome/4. Remote Control/5. Code/Main Code - Remote Control v1.0.c

/**
 * Name:     Smarthome: Remote Control
 * Autor:    Alberto Gil Tesa
 * Web:      https://giltesa.com/smarthome
 * License:  CC BY-NC-SA 3.0
 * Version:  1.1
 * Date:     2018/04/06
 *
 */



/**
 *  Pinout Remote Control V1.0
 */
#define pBTN        2 //Interruption
#define pNRF_CE     7
#define pNRF_CS    10
#define pLED_BLUE   9 //PWM
#define pATSHA204A A3



/**
 * MySensor configuration:
 */
//#define MY_DEBUG                        // Enable debug prints to serial monitor
#define MY_BAUD_RATE        9600        // Serial output baud rate
#define MY_RADIO_NRF24                  // Enable and select radio type attached
#define MY_RF24_CE_PIN      pNRF_CE     // Define this to change the chip enable pin from the default
#define MY_RF24_CS_PIN      pNRF_CS     // Define this to change the chip select pin from the default

#define MS_BOARD_NAME       "Remote Control"
#define MS_SOFTWARE_VERSION "1.1"
#define MS_BTN_CHILD_ID     0

#include <MySensors.h>

MyMessage msgBTN(MS_BTN_CHILD_ID, V_TRIPPED);



/**
 * For initialisations that needs to take place before MySensors transport has been setup (eg: SPI devices).
 */
void before()
{
    pinMode(pBTN,      INPUT_PULLUP);
    pinMode(pLED_BLUE, OUTPUT);

    digitalWrite(pLED_BLUE, HIGH);
    delay(3000);
    digitalWrite(pLED_BLUE, LOW);
}



/**
 * Called once at startup, usually used to initialize sensors.
 */
void setup()
{
}



/**
 * This allows controller to re-request presentation and do re-configuring node after startup.
 */
void presentation()
{
    sendSketchInfo(MS_BOARD_NAME, MS_SOFTWARE_VERSION);
    present(MS_BTN_CHILD_ID, S_DOOR, "Switch");
}



/**
 * This will be called continuously after setup.
 */
void loop()
{
    int valueSleep = sleep(digitalPinToInterrupt(pBTN), LOW, 0);

    if( valueSleep == MY_SLEEP_NOT_POSSIBLE )
    {
        #ifdef MY_DEBUG
            Serial.println(">>> Unable to sleep");
        #endif

        for( int i=0 ; i<3 ; i++ )
        {
            digitalWrite(pLED_BLUE, HIGH);
            wait(250);
            digitalWrite(pLED_BLUE, LOW);
            wait(100);
        }
    }
    else if( valueSleep == digitalPinToInterrupt(pBTN) )
    {
        #ifdef MY_DEBUG
            Serial.println(">>> Switch active");
        #endif

        digitalWrite(pLED_BLUE, HIGH);
        send(msgBTN.set(true));
        sendBatteryLevel(getBatteryLevel());
        wait(500);
        digitalWrite(pLED_BLUE, LOW);
    }
}



/**
 * https://forum.arduino.cc/index.php?topic=356752.0
 */
long getBatteryLevel()
{
    long result;
    // Read 1.1V reference against AVcc
    ADMUX = _BV(REFS0) | _BV(MUX3) | _BV(MUX2) | _BV(MUX1);
    delay(2); // Wait for Vref to settle
    ADCSRA |= _BV(ADSC); // Convert
    while( bit_is_set(ADCSRA,ADSC) );
    result = ADCL;
    result |= ADCH<<8;
    result = 1126400L / result; // Back-calculate AVcc in mV

    #ifdef MY_DEBUG
        Serial.print(">>> Battery: "); Serial.println(result);
    #endif

    return result;
}
